DEADROSE6/FdD_Equipo_8/FundDiseño/Talleres/Taller_10/Onshape Areche Angello/bryam-areche-4c7b2a17-952c-4959-8db5-8d5ba8efbf5f-certificate.pdf

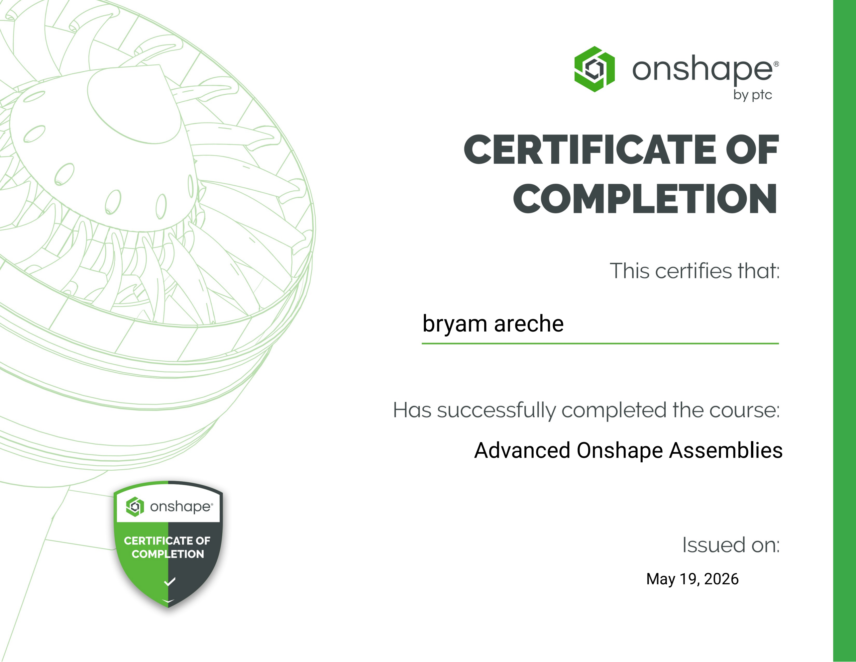
[picture p7: page 1]

bryam areche

Advanced Onshape Assemblies

May 19, 2026
