DEADROSE6/FdD_Equipo_8/Proyecto/MóduloMecánico/Certificados/Leslie Tomanguilla/CAD Basic.pdf

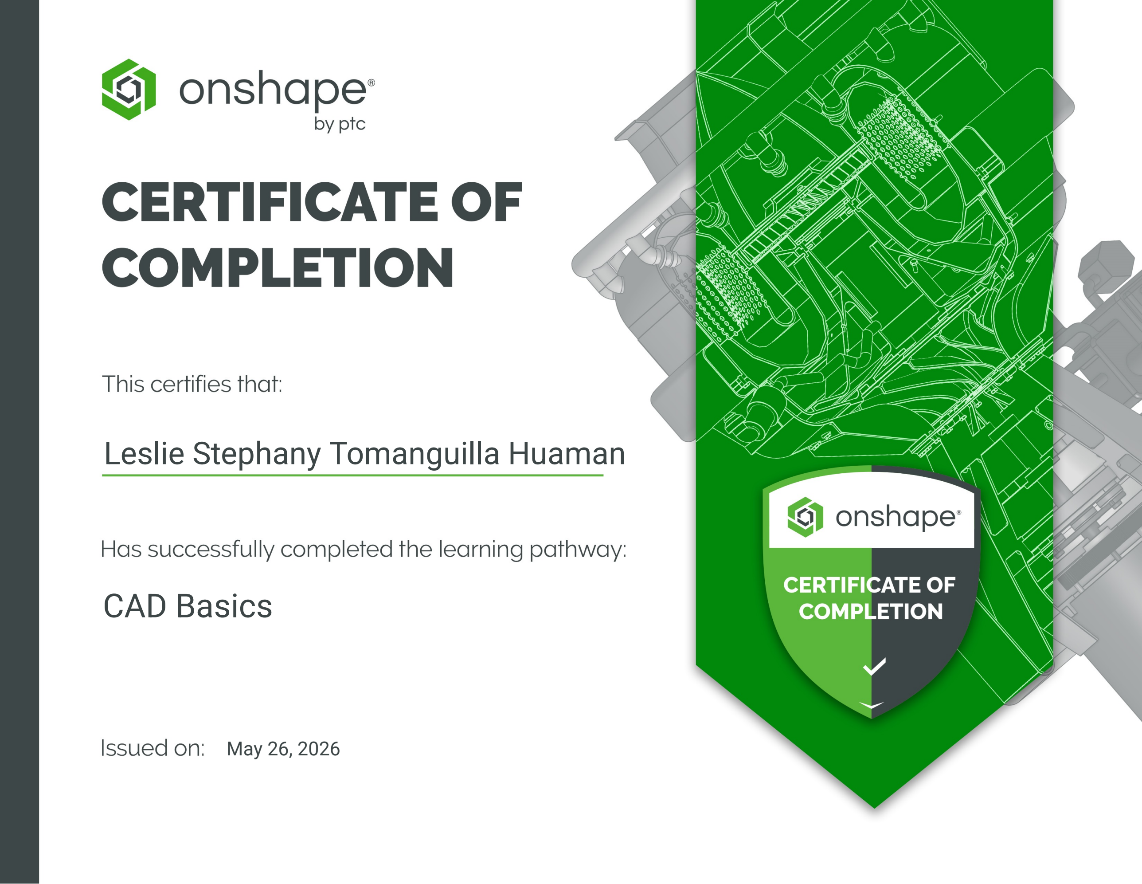
[picture p8: page 1]

Leslie Stephany Tomanguilla Huaman

CAD Basics

May 26, 2026
