DEADROSE6/FdD_Equipo_8/Proyecto/MóduloMecánico/Certificados/Daniela Mori/introduction-to-onshape-mori.pdf

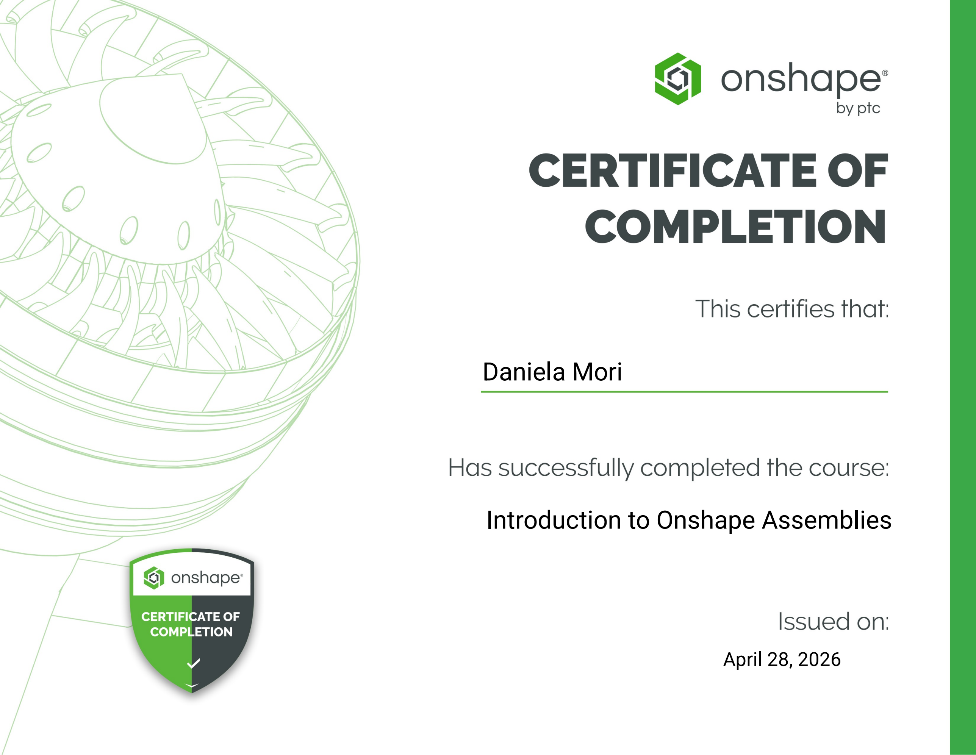
[picture p9: page 1]

Daniela Mori

April 28, 2026

Introduction to Onshape Assemblies
