DEADROSE6/FdD_Equipo_8/Proyecto/MóduloMecánico/Certificados/Leslie Tomanguilla/Advanced Onshape Assamblies.pdf

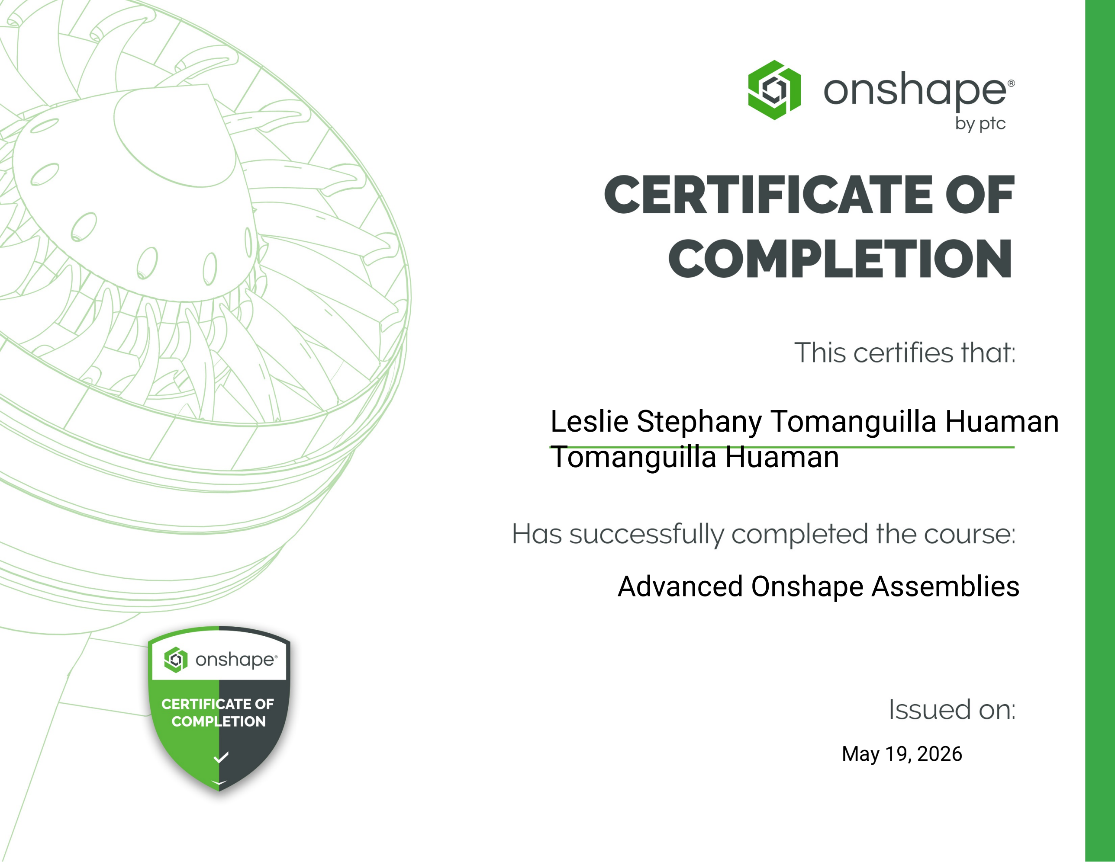
[picture p10: page 1]

Leslie Stephany Tomanguilla Huaman Tomanguilla Huaman

Advanced Onshape Assemblies

May 19, 2026
