DEADROSE6/FdD_Equipo_8/Proyecto/MóduloMecánico/Certificados/Rolando Ronceros/Advanced Onshape Assamblies.pdf

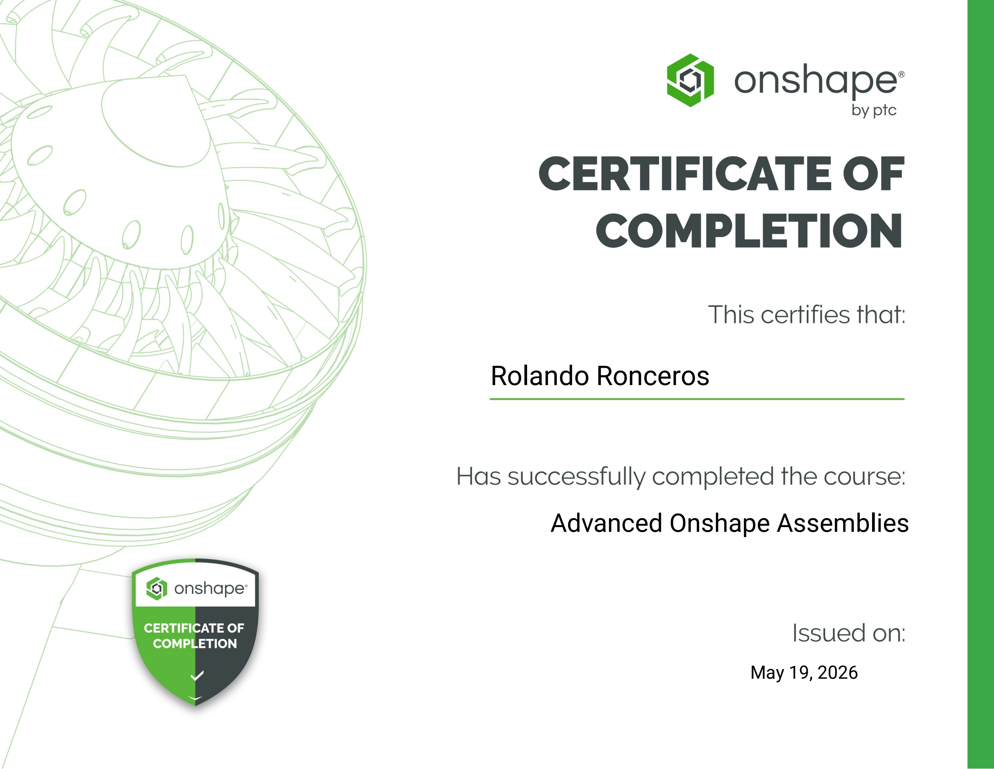
[picture p11: page 1]

Rolando Ronceros

Advanced Onshape Assemblies

May 19, 2026
