DEADROSE6/FdD_Equipo_8/Proyecto/MóduloMecánico/Certificados/Daniela Mori/CAD-Basics-mori.pdf

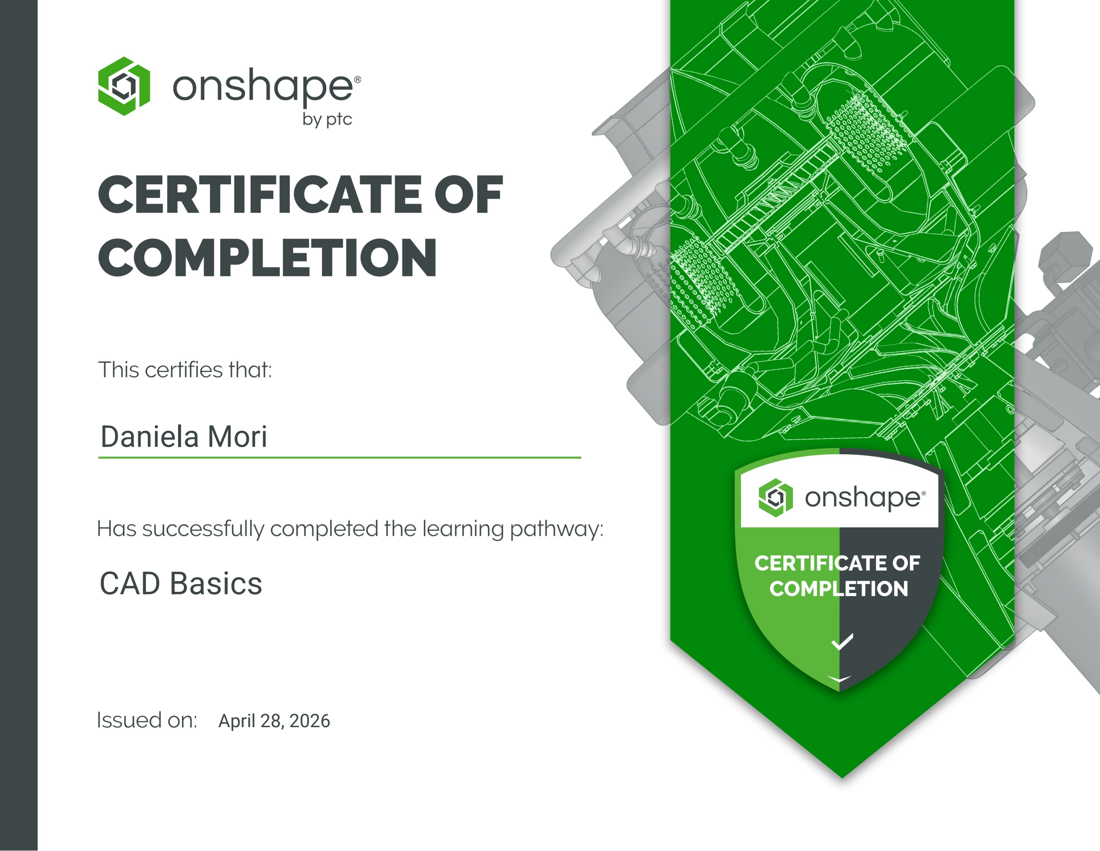
[picture p12: page 1]

## Daniela Mori

# CAD Basics

April 28, 2026
