DEADROSE6/FdD_Equipo_8/Proyecto/MóduloMecánico/Certificados/Rolando Ronceros/CAD Basic (1).pdf

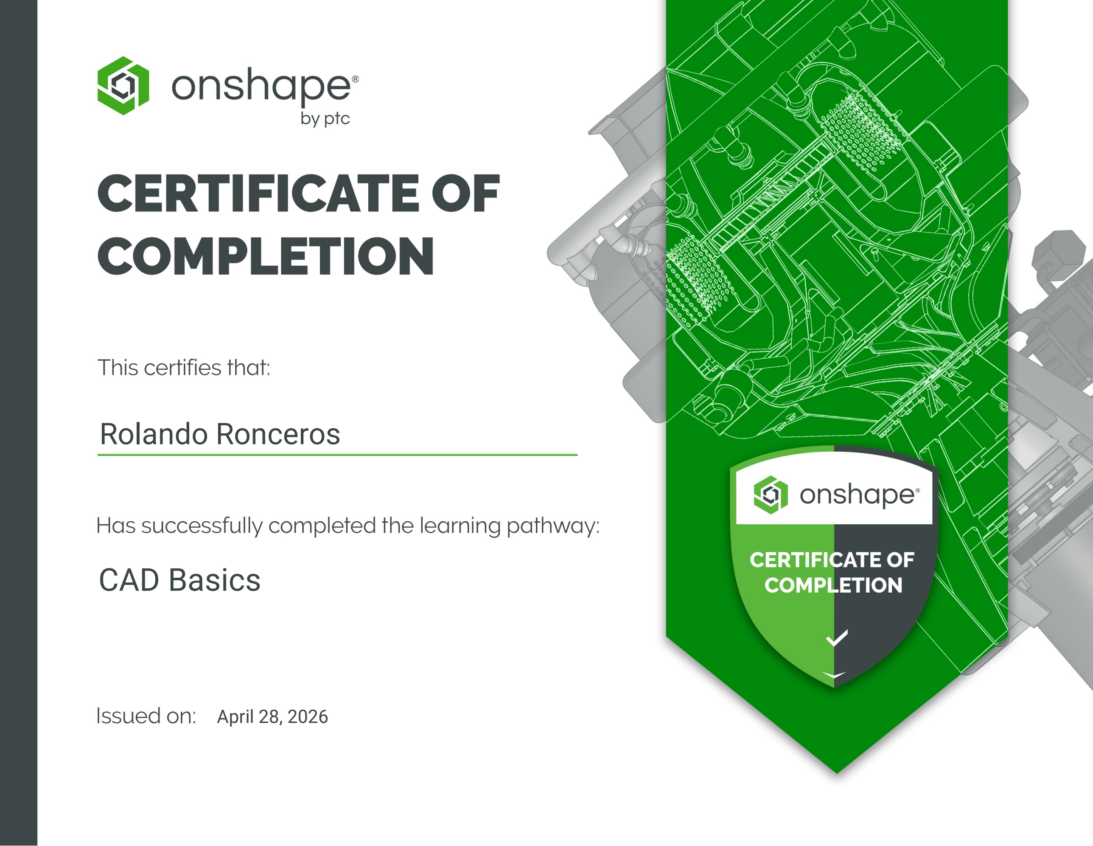
[picture p13: page 1]

Rolando Ronceros

CAD Basics

April 28, 2026
