DEADROSE6/FdD_Equipo_8/Proyecto/MóduloMecánico/Certificados/Alex Ccoyllo/CAD Basic.pdf

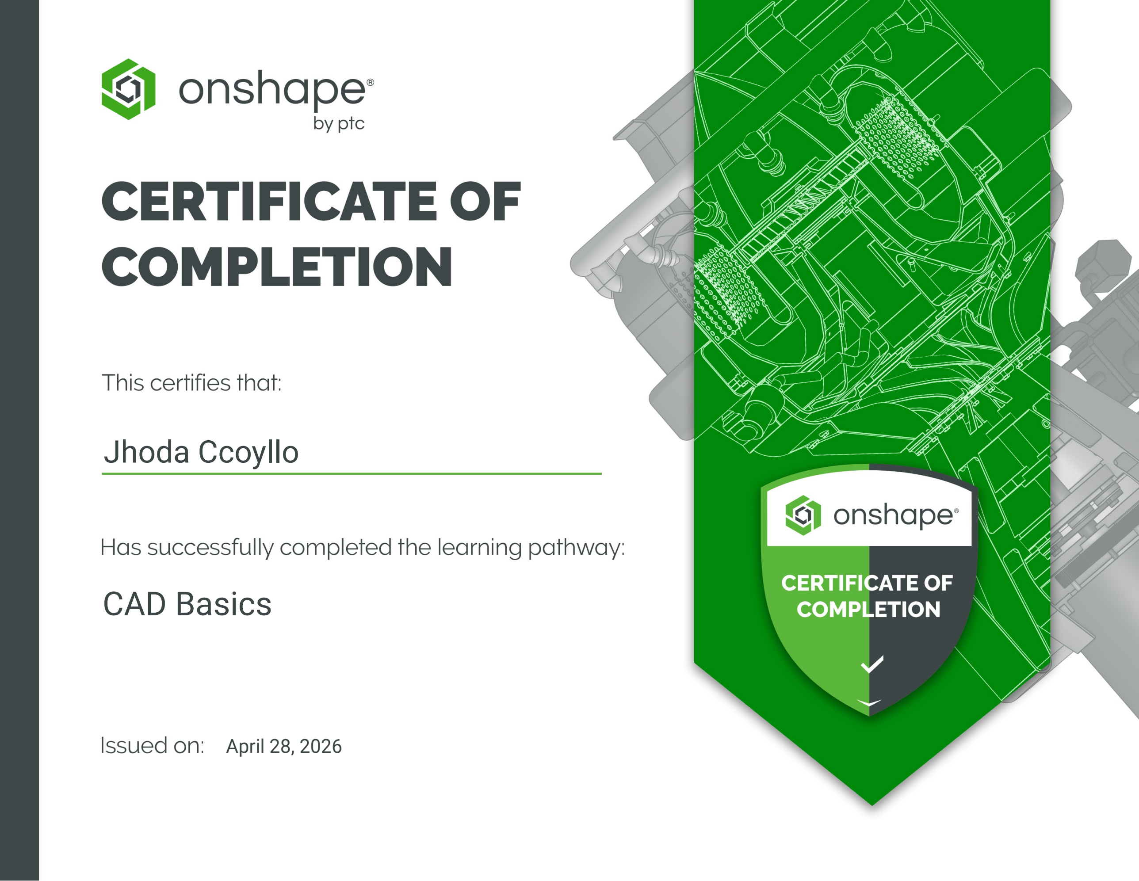
[picture p14: page 1]

## Jhoda Ccoyllo

# CAD Basics

April 28, 2026
