DEADROSE6/FdD_Equipo_8/FundDiseño/Entregables/Entregables_3/Bocetos/Prompt del Boceto (1).pdf

Dibujo técnico simple en blanco y negro sobre fondo completamente blanco, estilo boceto de ingeniería hecho a mano con líneas limpias. Mostrar tres vistas separadas de una caja electrónica.

Primera vista (vista frontal interna): caja rectangular abierta vista desde arriba. Señalar con flechas y texto los componentes: 'Amplificador de audio (PAM8403)' ubicado en el centro-izquierda, 'DF Player MP3' en la parte superior derecha de una placa central, 'Sensor de distancia (VL53L1X)' debajo a la derecha del PAM8403 y 'Sensor de presencia humana (LD2410C)' en la parte inferior. Mantener diseño simple y esquemático.

Segunda vista (Vista lateral derecho): vista lateral de la caja mostrando rejillas de ventilación y un altavoz circular. Señalar únicamente 'Altavoz'. Título arriba: 'Vista lateral derecho'.

Tercera vista (Vista isométrica): perspectiva isométrica de la misma caja mostrando los componentes internos. Añadir una flecha apuntando a una cámara con la etiqueta 'Cámara (OV3660) con XIAO SEED'. Título arriba: 'Vista isométrica'.

Estilo minimalista, líneas negras finas, sin colores, sin sombras, sin borde decorativo, sin marco rojo, aspecto de plano escolar limpio, distribución similar a un dibujo técnico realizado a lápiz sobre una hoja blanca.
