DEADROSE6/FdD_Equipo_8/FundDiseño/Talleres/Taller mecánico de ONSHAPE/Certificado de angello/Onshape_Fundamentals.pdf

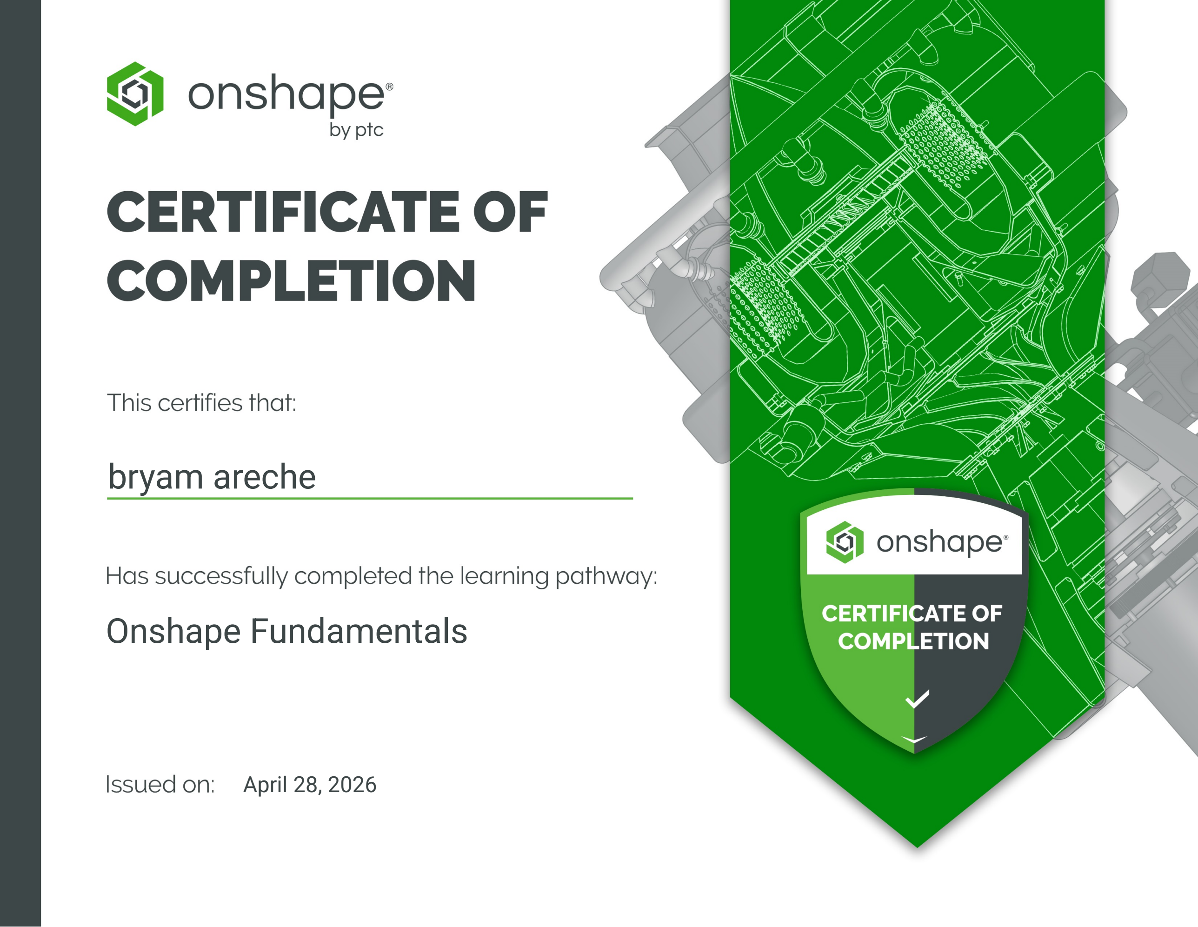
[picture p61: page 1]

Onshape Fundamentals

April 28, 2026

bryam areche
