DEADROSE6/FdD_Equipo_8/Recursos/Productos comerciales/Brochure2_WeWALK.pdf

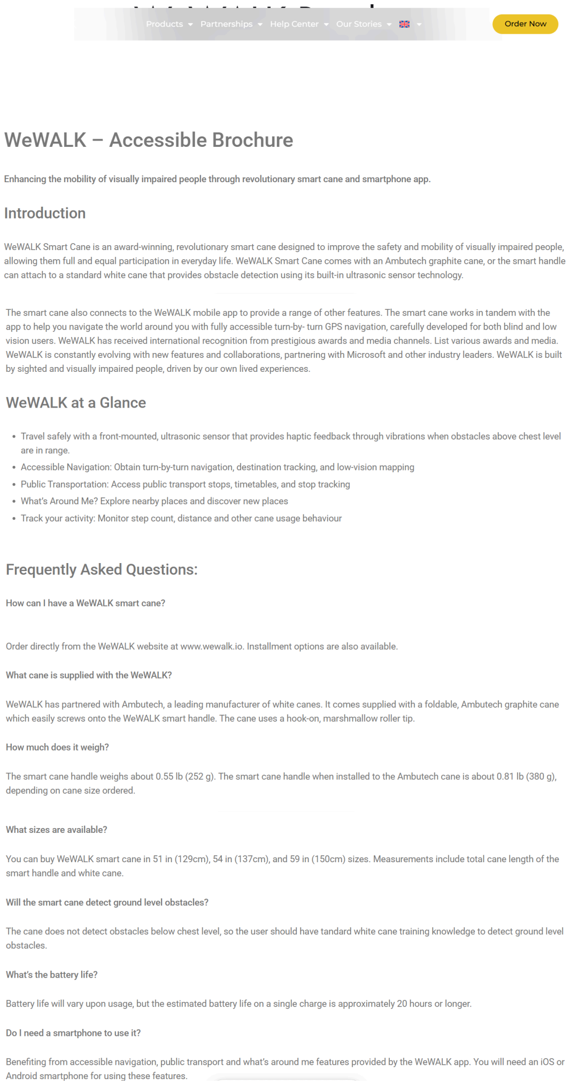
[picture p62: page 1]

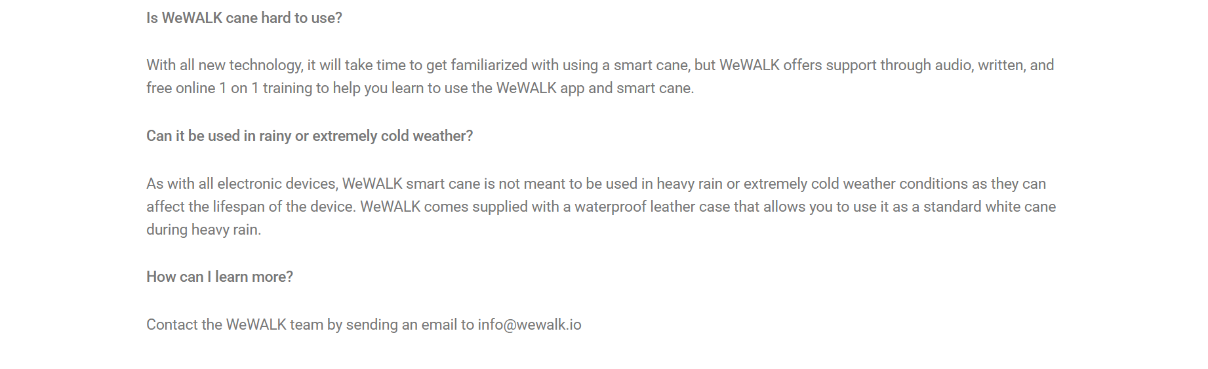
[picture p63: figure]
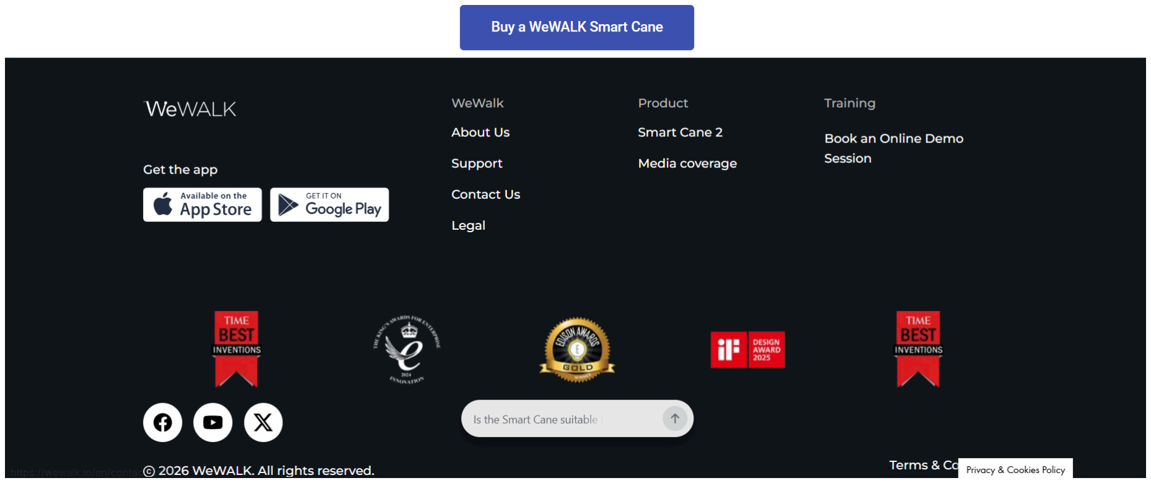
[picture p64: figure]
