DEADROSE6/FdD_Equipo_8/Proyecto/MóduloMecánico/V.FINAL/BocetoIA.pdf

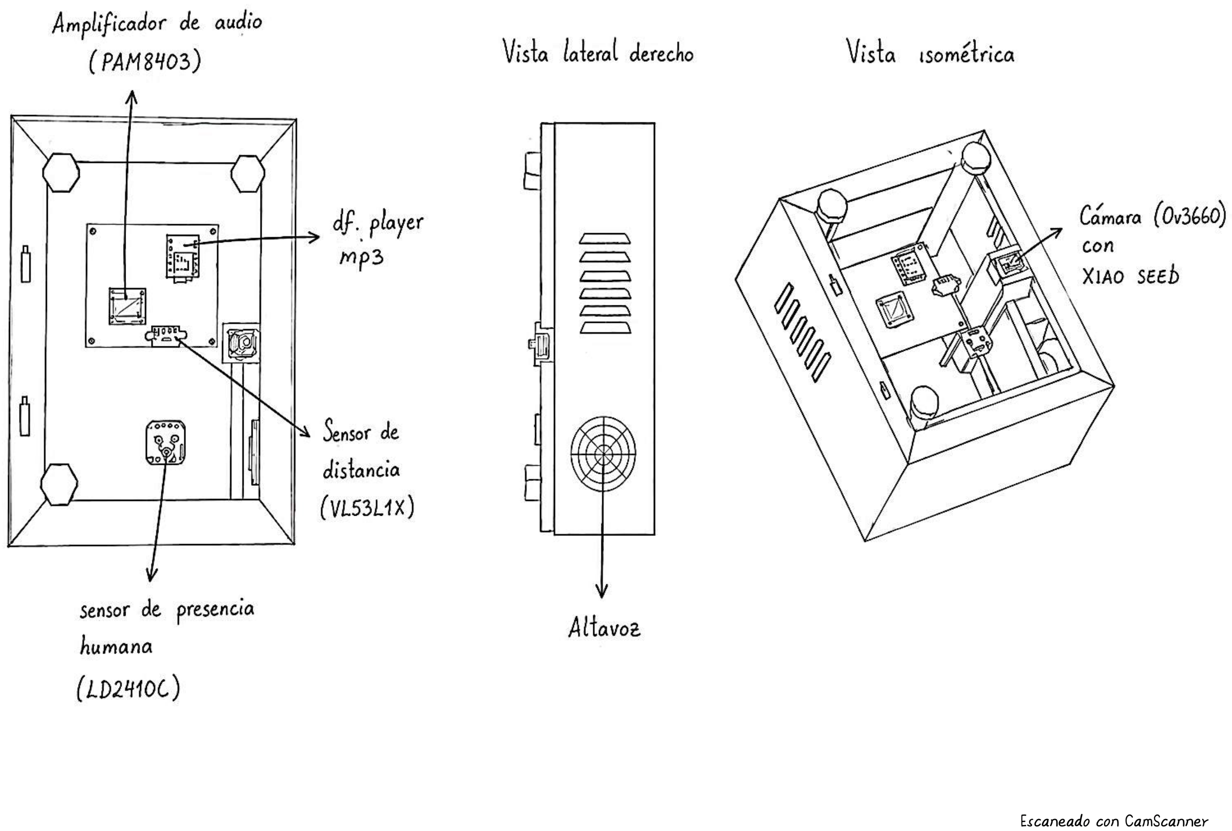
[picture p65: page 1]
