DEADROSE6/FdD_Equipo_8/Proyecto/MóduloMecánico/V.FINAL/BocetoIA2.pdf

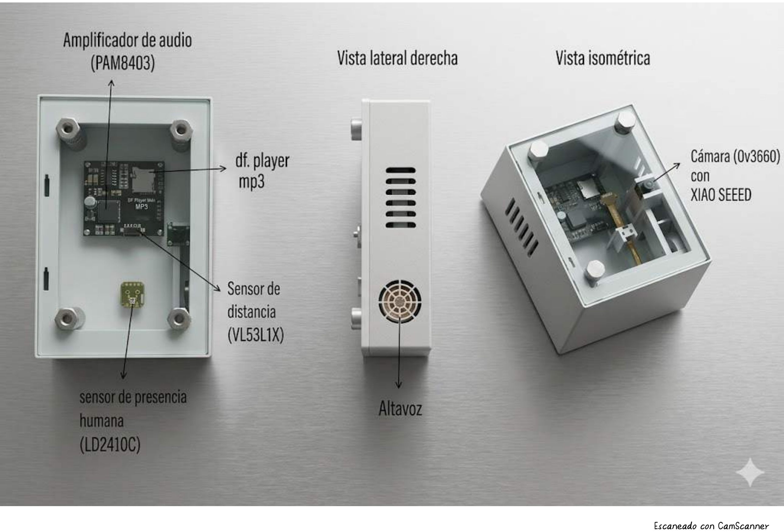
[picture p66: page 1]
