DEADROSE6/FdD_Equipo_8/Proyecto/MóduloMecánico/V.FINAL/BocetoLapiz.pdf

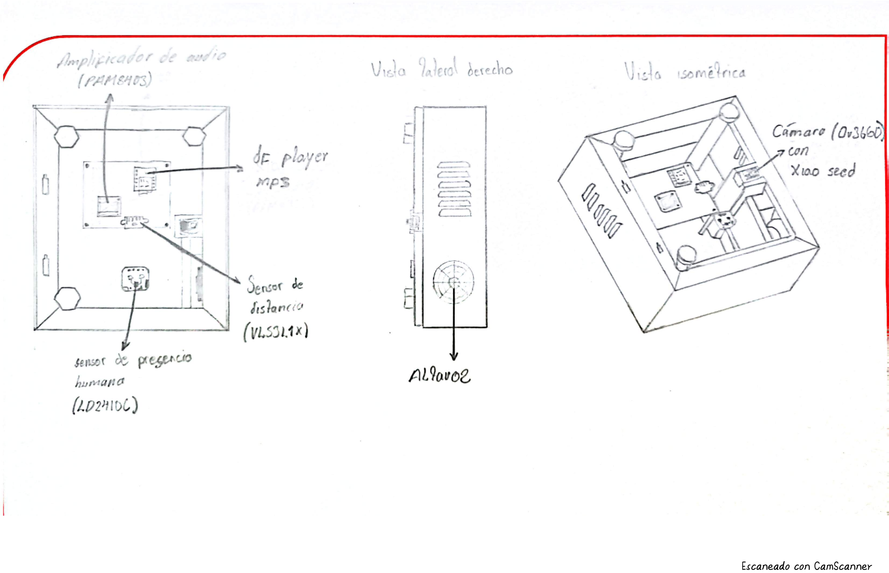
[picture p67: page 1]
