DEADROSE6/FdD_Equipo_8/Proyecto/MóduloMecánico/Certificados/Leslie Tomanguilla/Detailed Drawings.pdf

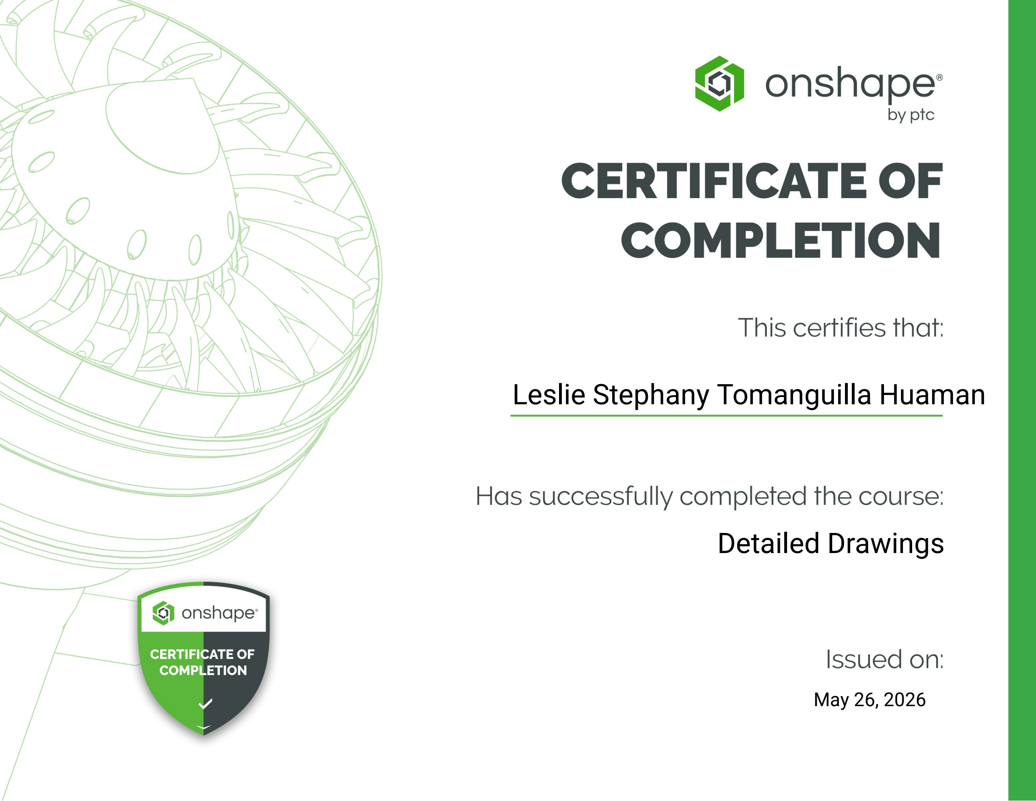
[picture p68: page 1]

Leslie Stephany Tomanguilla Huaman

May 26, 2026

Detailed Drawings
