DEADROSE6/FdD_Equipo_8/Proyecto/MóduloMecánico/Certificados/Leslie Tomanguilla/Introduction to Drawings.pdf

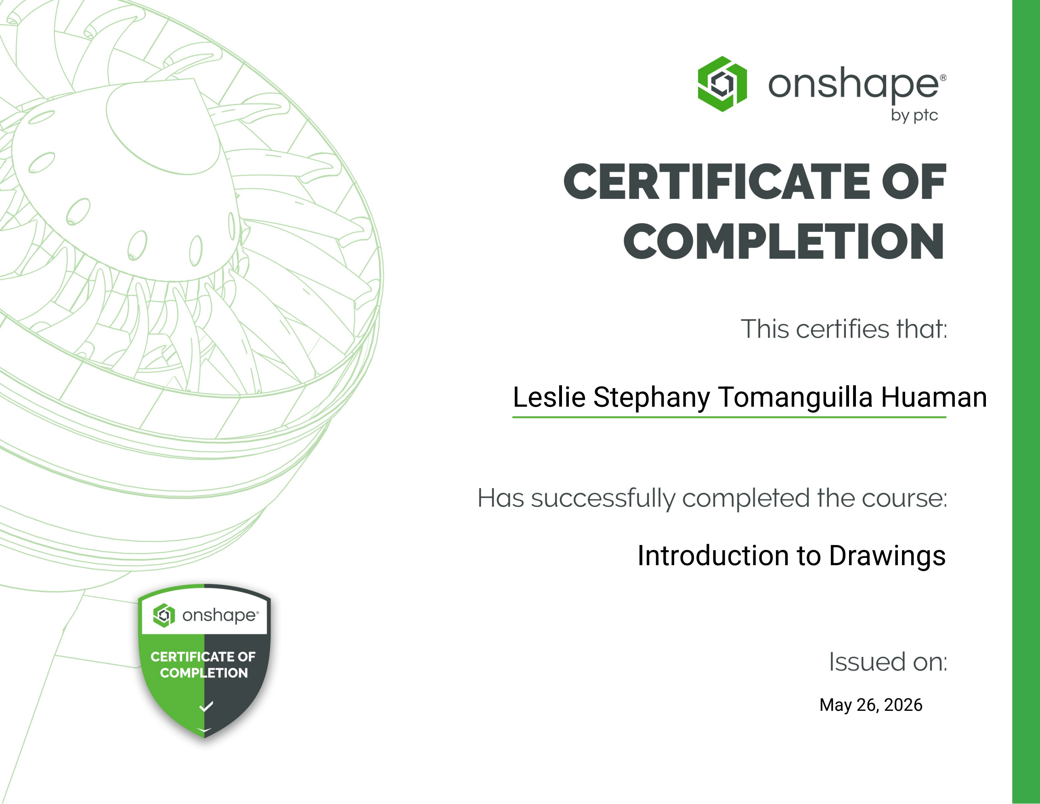
[picture p69: page 1]

Leslie Stephany Tomanguilla Huaman

May 26, 2026

Introduction to Drawings
