DEADROSE6/FdD_Equipo_8/Proyecto/MóduloMecánico/Certificados/Leslie Tomanguilla/Introduction to Part Studios.pdf

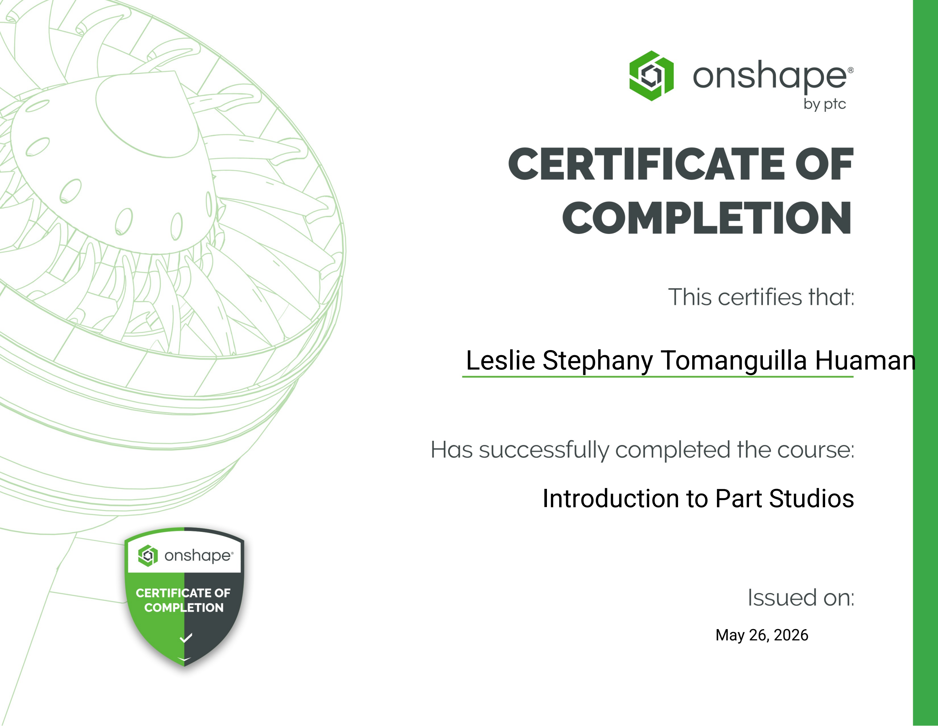
[picture p70: page 1]

Leslie Stephany Tomanguilla Huaman

Introduction to Part Studios

May 26, 2026
