DEADROSE6/FdD_Equipo_8/Proyecto/MóduloMecánico/Certificados/Leslie Tomanguilla/Introduction to Sketching.pdf

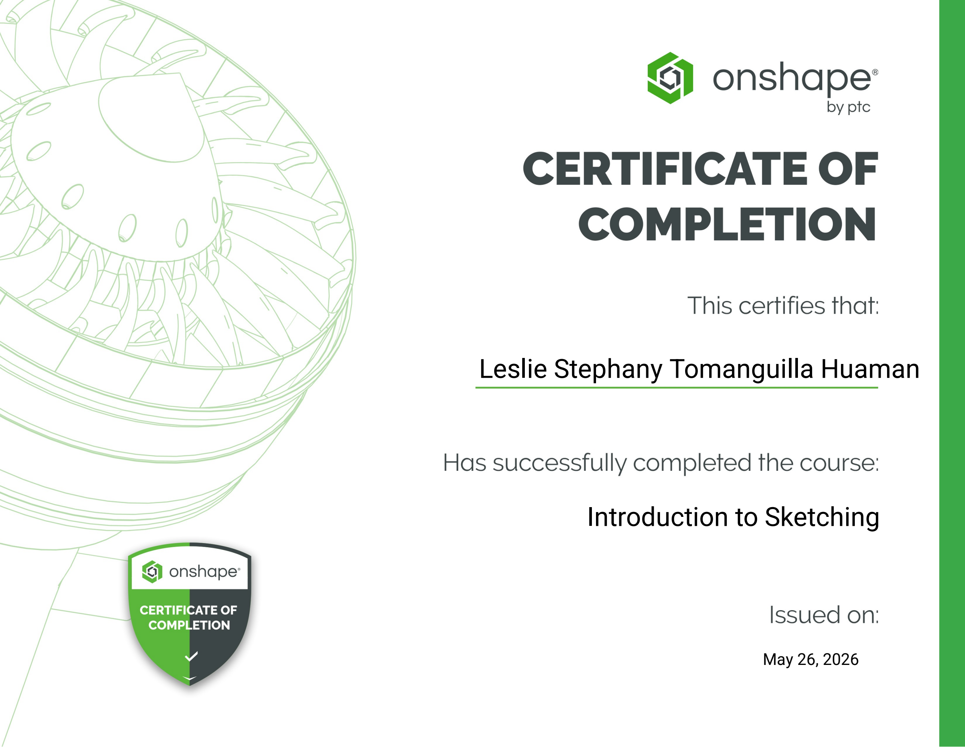
[picture p71: page 1]

Leslie Stephany Tomanguilla Huaman

Introduction to Sketching

May 26, 2026
