DEADROSE6/FdD_Equipo_8/Proyecto/MóduloMecánico/Certificados/Leslie Tomanguilla/Onshape Fundamentals.pdf

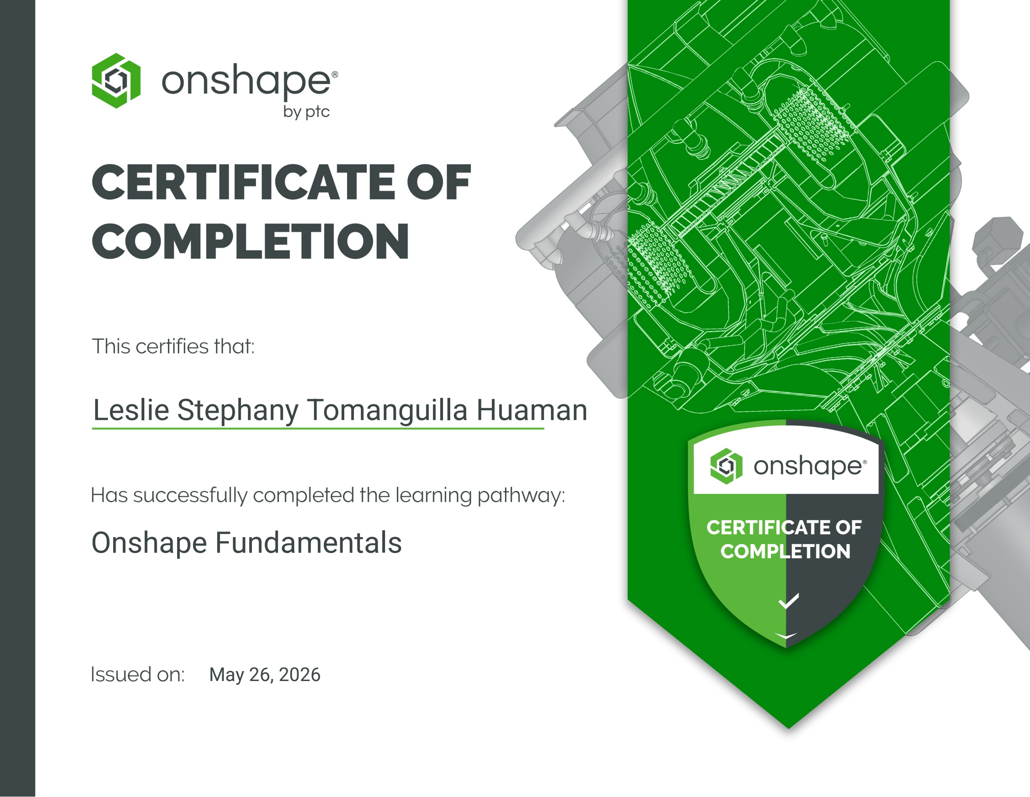
[picture p72: page 1]

Onshape Fundamentals

May 26, 2026

Leslie Stephany Tomanguilla Huaman
