DEADROSE6/FdD_Equipo_8/Proyecto/MóduloMecánico/Certificados/Daniela Mori/detailed-drawings-mori.pdf

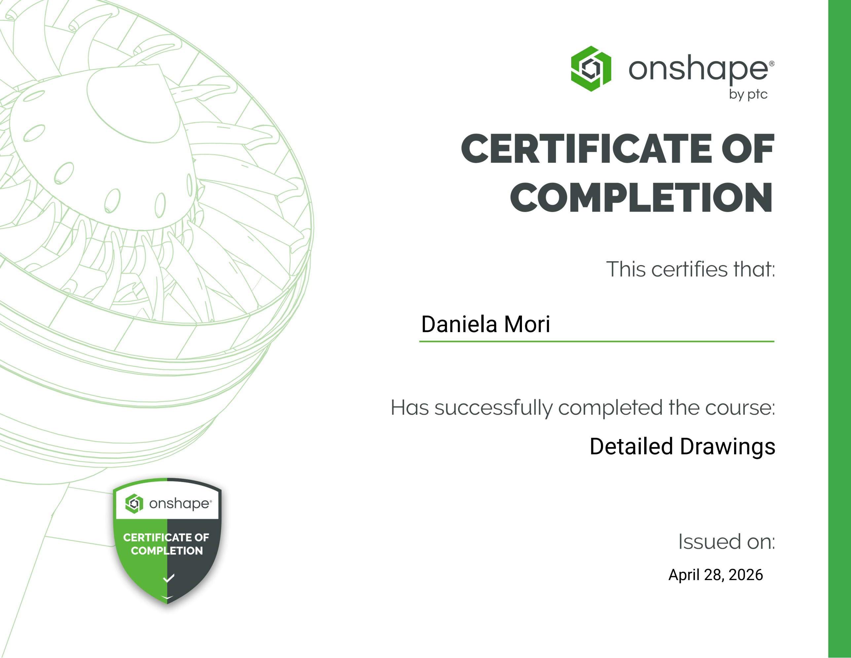
[picture p73: page 1]

Daniela Mori

April 28, 2026

Detailed Drawings
