DEADROSE6/FdD_Equipo_8/Proyecto/MóduloMecánico/Certificados/Daniela Mori/introduccion-to-drawings-mori.pdf

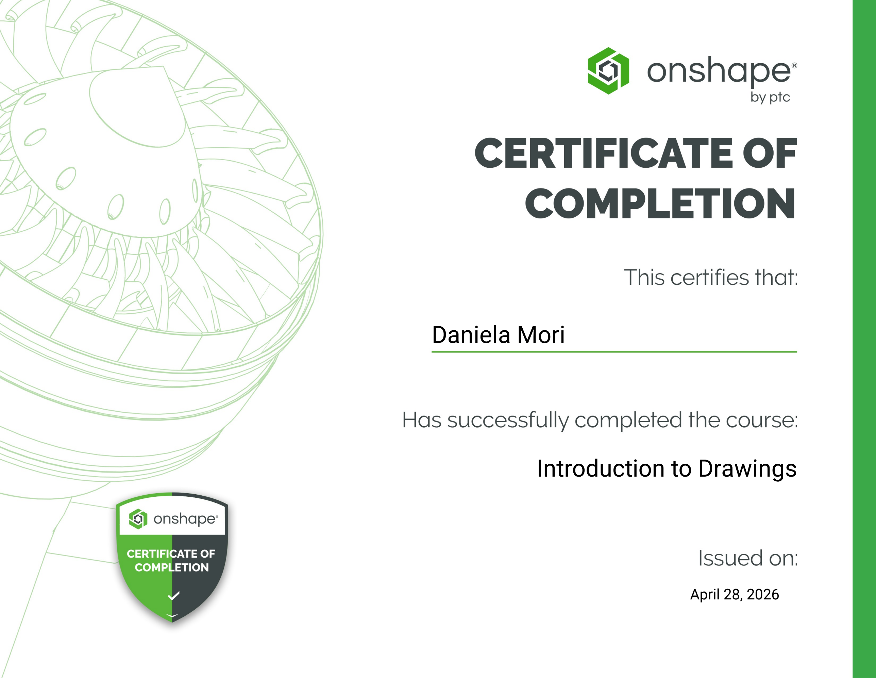
[picture p74: page 1]

Daniela Mori

April 28, 2026

Introduction to Drawings
