DEADROSE6/FdD_Equipo_8/Proyecto/MóduloMecánico/Certificados/Daniela Mori/Introduction to Part Studios-mori.pdf

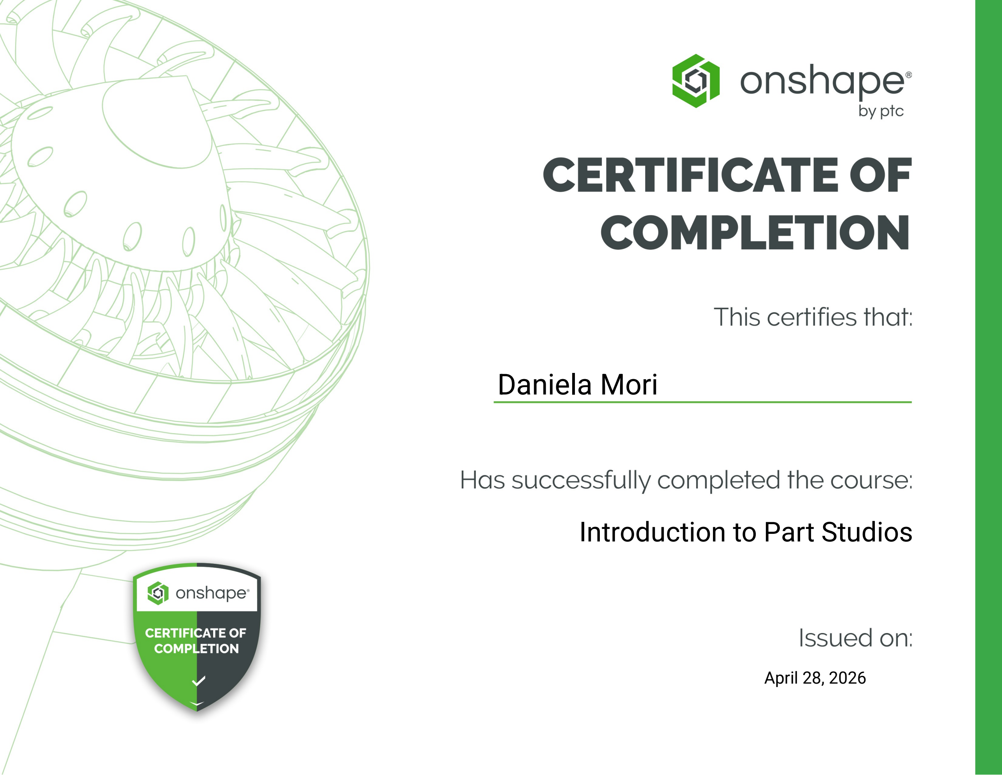
[picture p75: page 1]

Daniela Mori

Introduction to Part Studios

April 28, 2026
