DEADROSE6/FdD_Equipo_8/Proyecto/MóduloMecánico/Certificados/Daniela Mori/introduction-to-skeching-mori.pdf

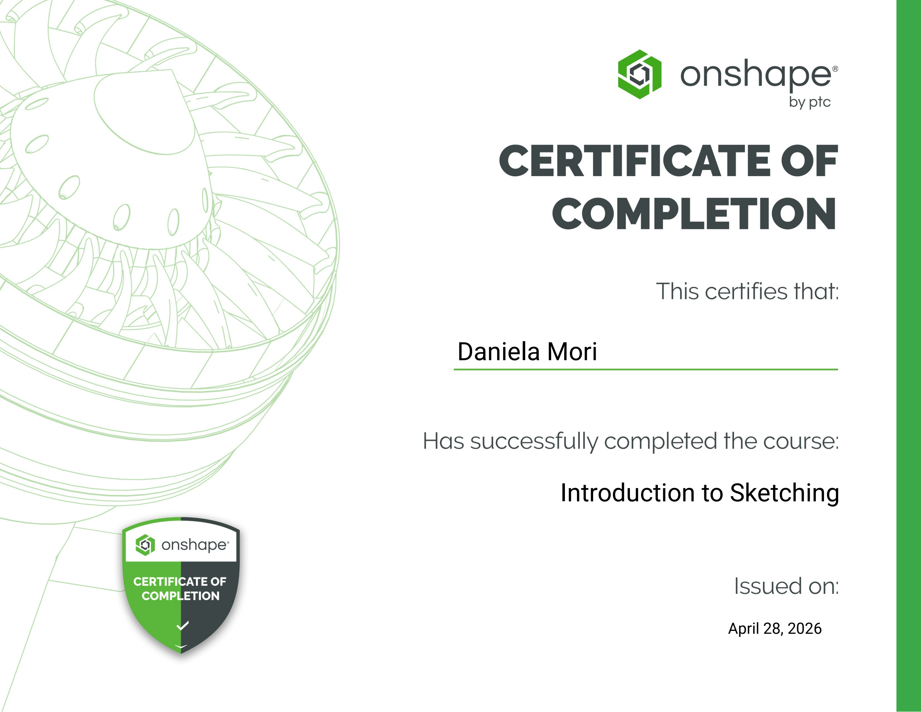
[picture p76: page 1]

Daniela Mori

Introduction to Sketching

April 28, 2026
