DEADROSE6/FdD_Equipo_8/Proyecto/MóduloMecánico/Certificados/Alex Ccoyllo/Detailed Drawings.pdf

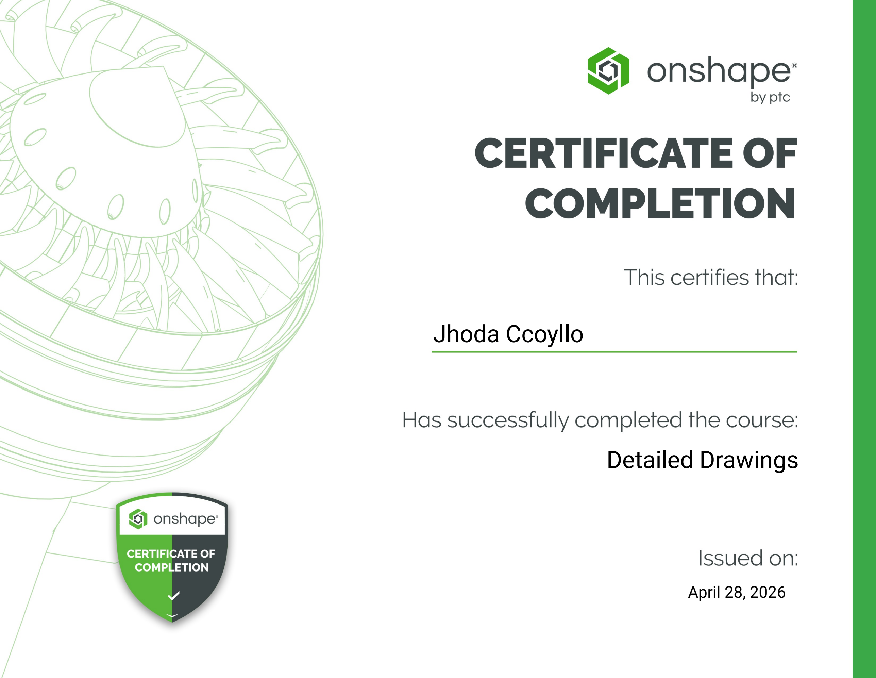
[picture p77: page 1]

Jhoda Ccoyllo

April 28, 2026

Detailed Drawings
