DEADROSE6/FdD_Equipo_8/Proyecto/MóduloMecánico/Certificados/Alex Ccoyllo/Introduction  to Sketching.pdf

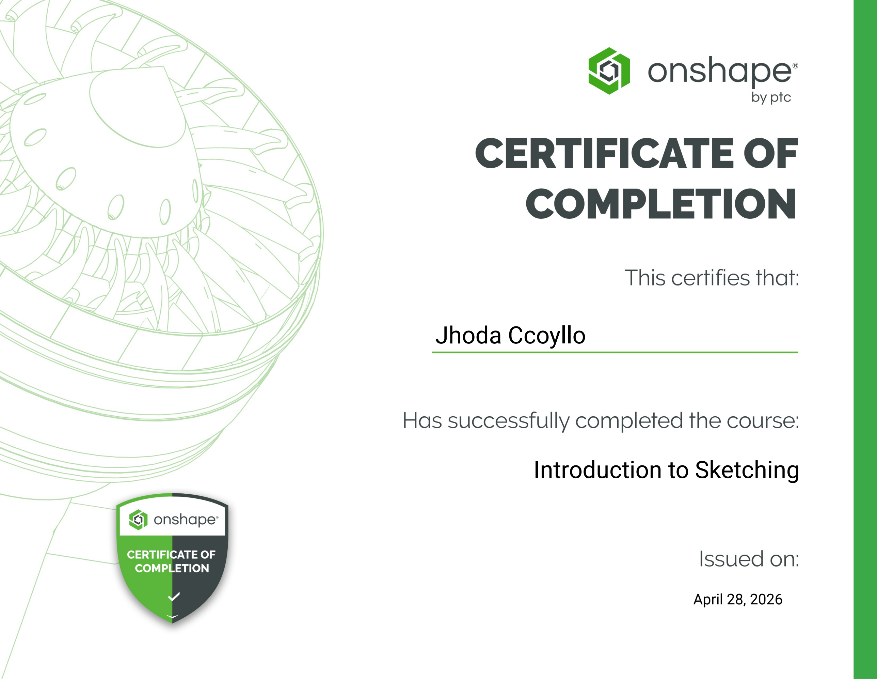
[picture p78: page 1]

Jhoda Ccoyllo

Introduction to Sketching

April 28, 2026
