DEADROSE6/FdD_Equipo_8/Proyecto/MóduloMecánico/Certificados/Alex Ccoyllo/Introductionto Drawings.pdf

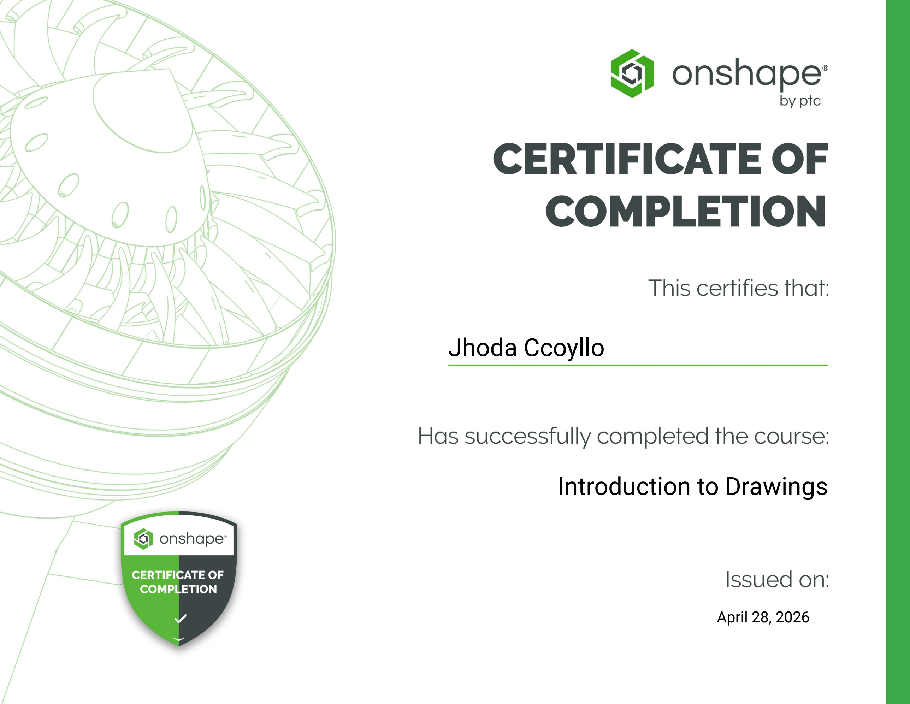
[picture p79: page 1]

Jhoda Ccoyllo

April 28, 2026

Introduction to Drawings
