DEADROSE6/FdD_Equipo_8/Proyecto/MóduloMecánico/Certificados/Alex Ccoyllo/Introductionto Part Studios.pdf

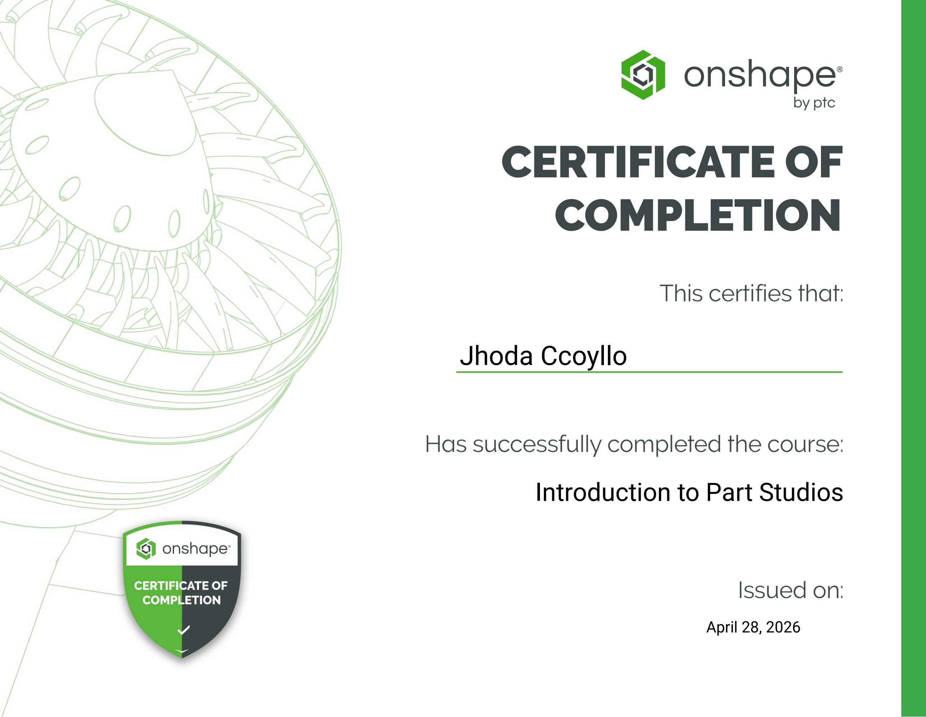
[picture p80: page 1]

Jhoda Ccoyllo

Introduction to Part Studios

April 28, 2026
