DEADROSE6/FdD_Equipo_8/Proyecto/MóduloMecánico/Certificados/Rolando Ronceros/Detailed Drawings (1).pdf

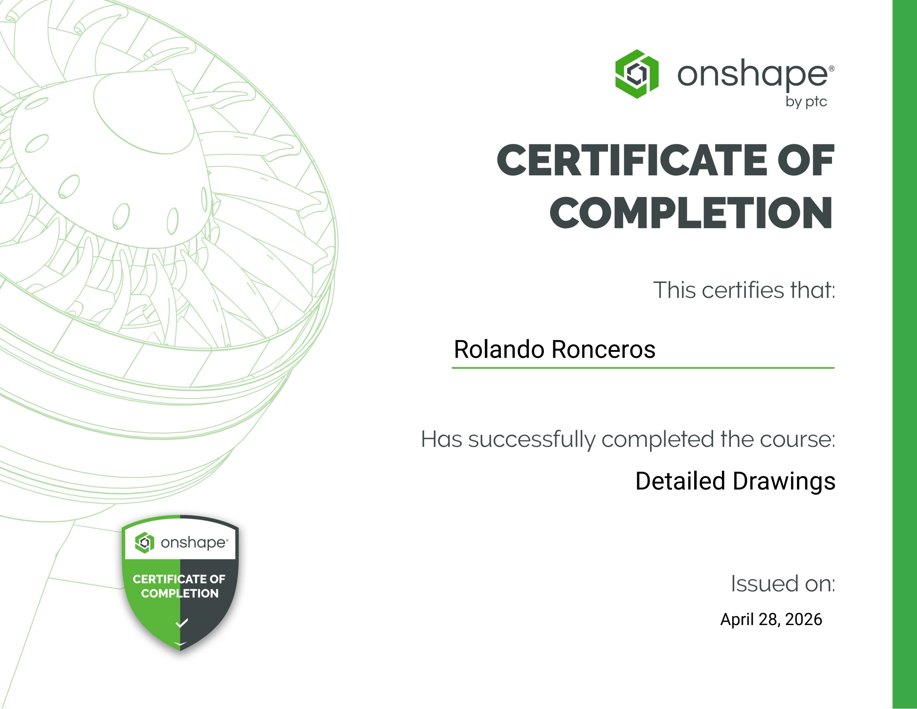
[picture p81: page 1]

Rolando Ronceros

April 28, 2026

Detailed Drawings
