DEADROSE6/FdD_Equipo_8/Proyecto/MóduloMecánico/Certificados/Rolando Ronceros/Introduction to Drawings.pdf

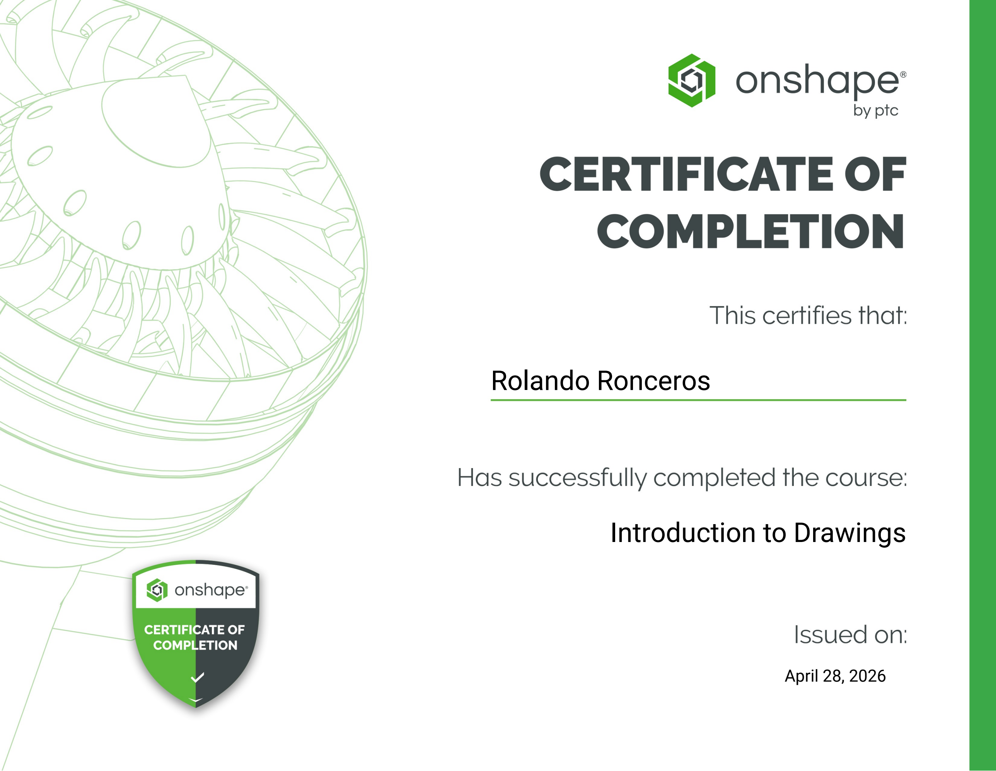
[picture p82: page 1]

Rolando Ronceros

April 28, 2026

Introduction to Drawings
