DEADROSE6/FdD_Equipo_8/Proyecto/MóduloMecánico/Certificados/Rolando Ronceros/Introduction to Part Studios.pdf

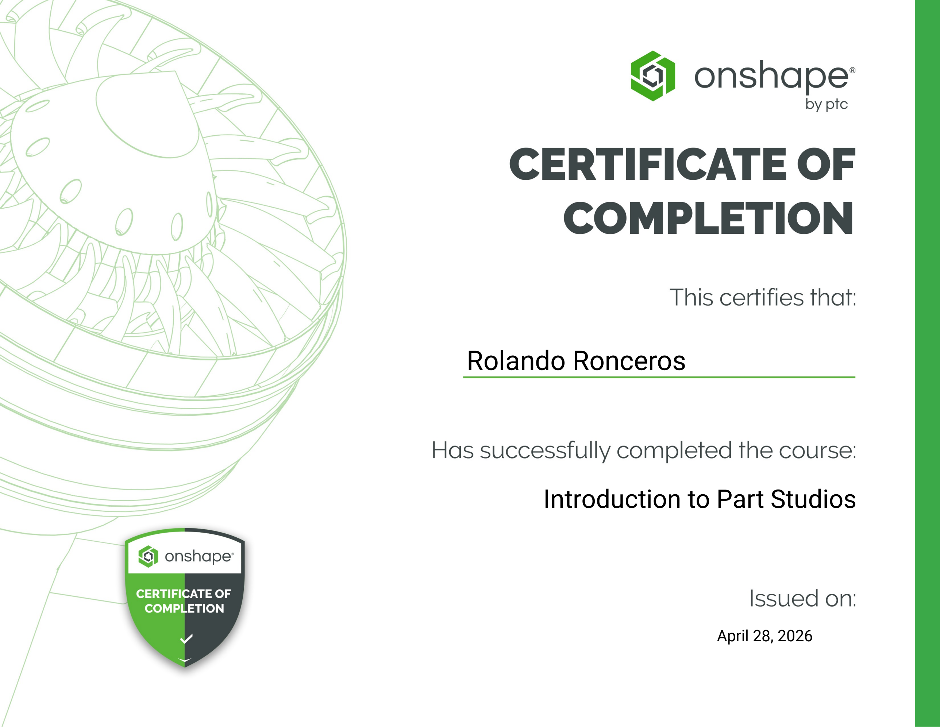
[picture p83: page 1]

Rolando Ronceros

Introduction to Part Studios

April 28, 2026
