DEADROSE6/FdD_Equipo_8/Proyecto/MóduloMecánico/Certificados/Rolando Ronceros/Introduction to Sketching.pdf

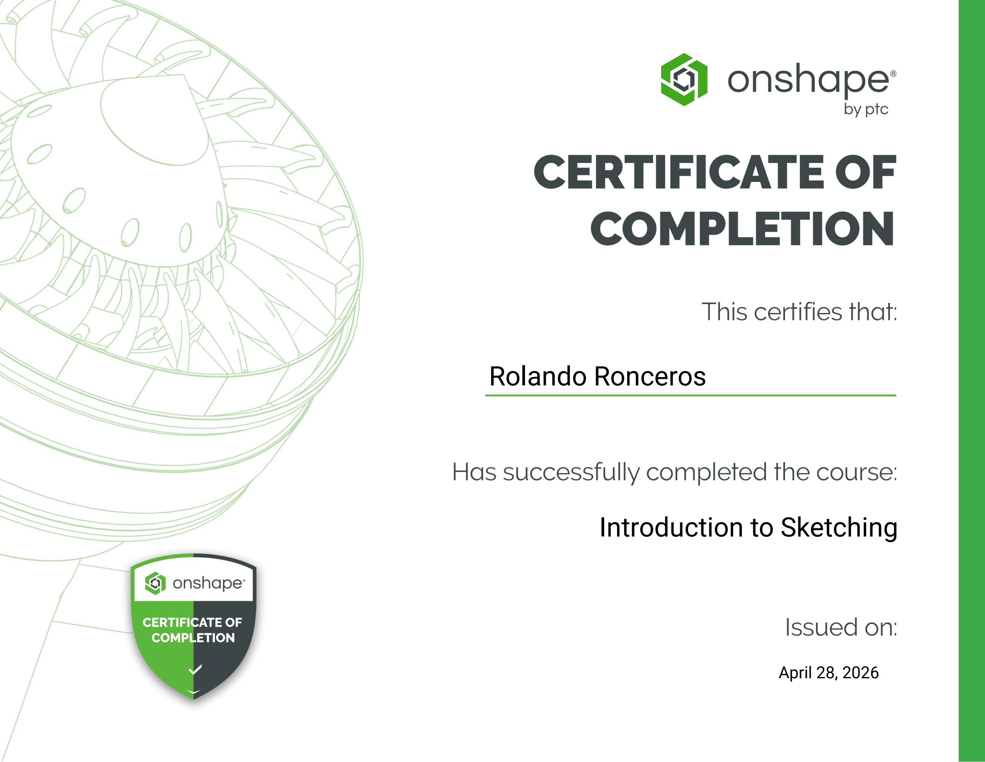
[picture p84: page 1]

Rolando Ronceros

Introduction to Sketching

April 28, 2026
