DEADROSE6/FdD_Equipo_8/Proyecto/MóduloMecánico/Certificados/Daniela Mori/onshape-fundamentals-mori.pdf

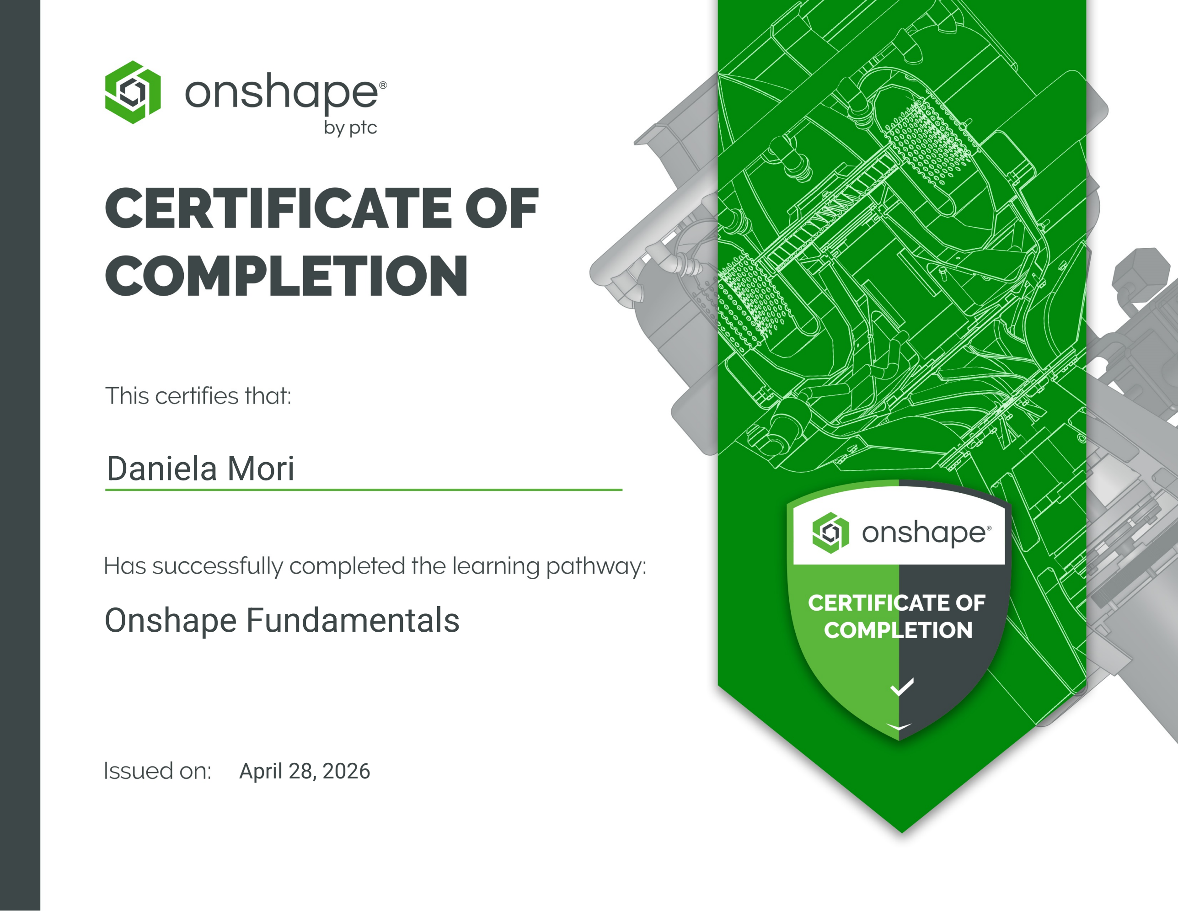
[picture p85: page 1]

Onshape Fundamentals

April 28, 2026

Daniela Mori
