DEADROSE6/FdD_Equipo_8/Proyecto/MóduloMecánico/Certificados/Rolando Ronceros/Onshape Fundamentals (1).pdf

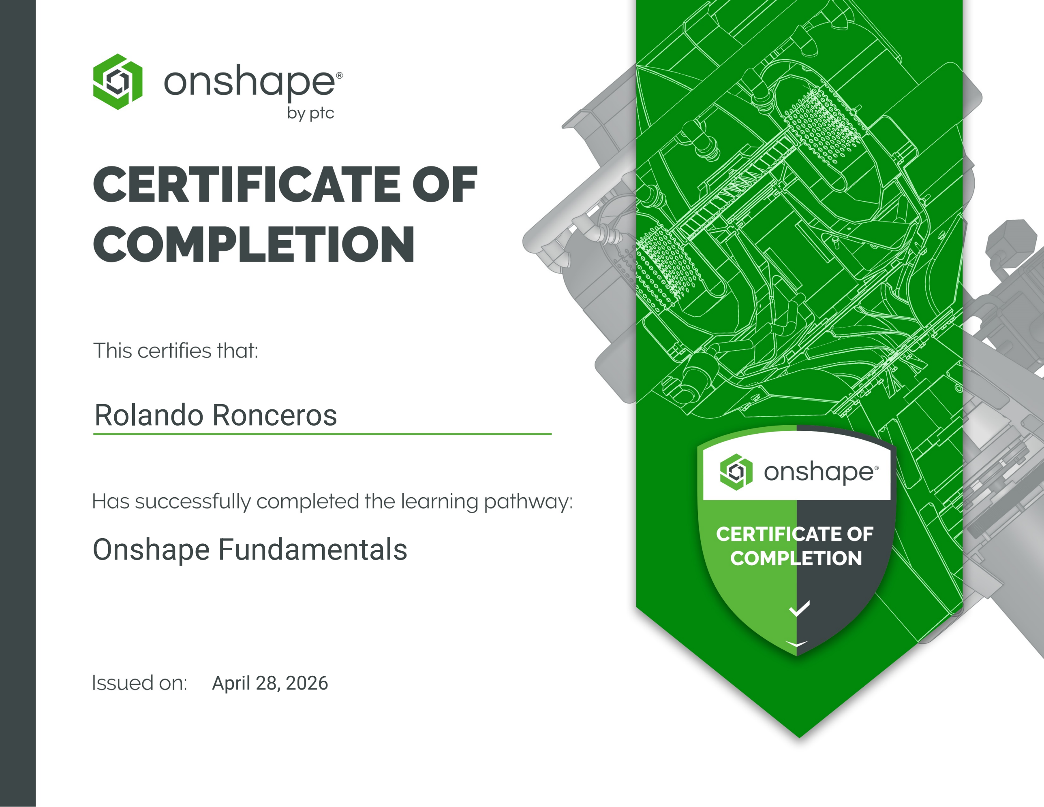
[picture p86: page 1]

Onshape Fundamentals

April 28, 2026

Rolando Ronceros
