DEADROSE6/FdD_Equipo_8/Proyecto/MóduloMecánico/Certificados/Alex Ccoyllo/Onshape Fundamentals.pdf

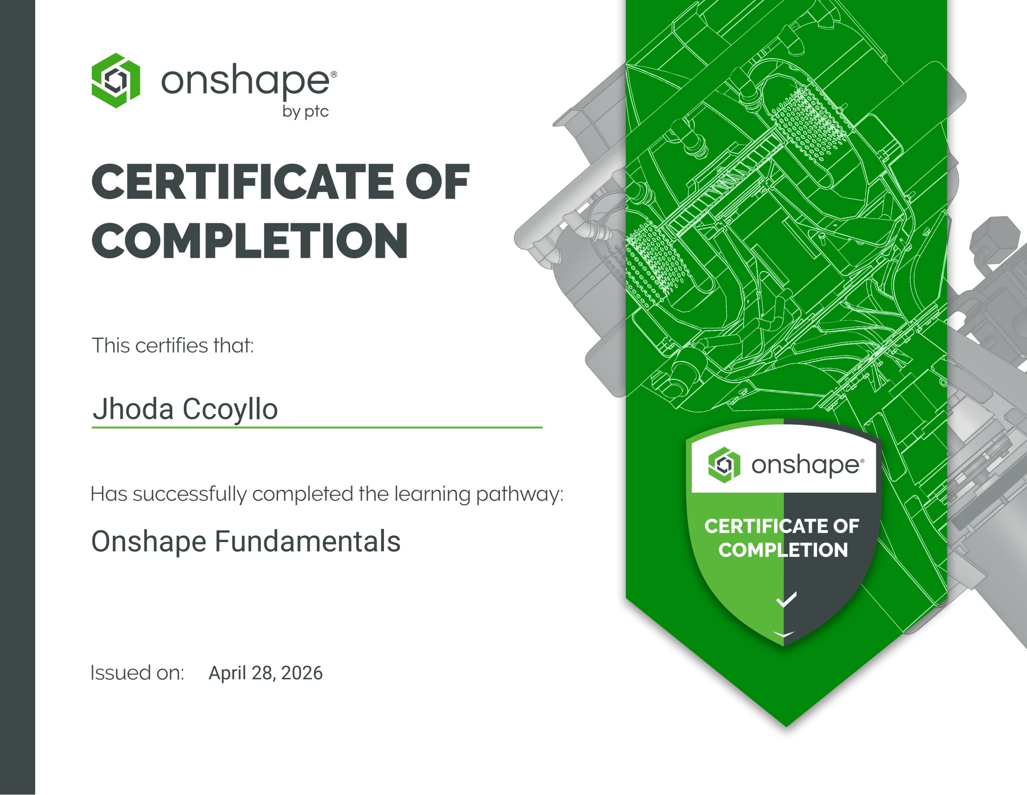
[picture p87: page 1]

Onshape Fundamentals

April 28, 2026

Jhoda Ccoyllo
