DEADROSE6/FdD_Equipo_8/FundDiseño/Talleres/Taller mecánico de ONSHAPE/Certificado de angello/Advanced Onshape Assamblies.pdf

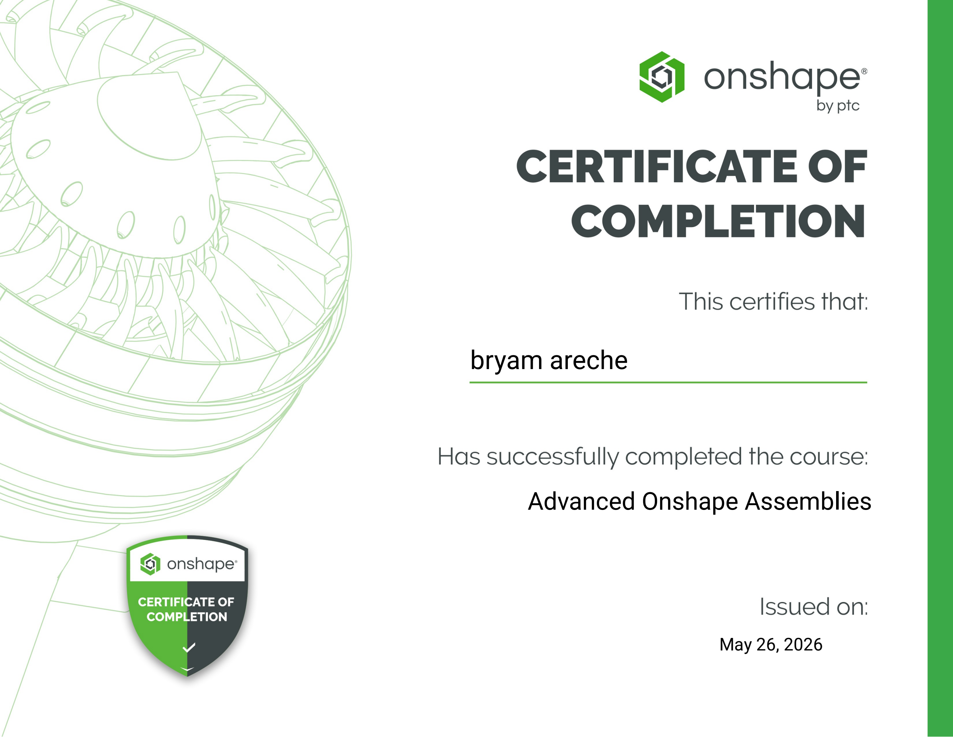
[picture p88: page 1]

bryam areche

Advanced Onshape Assemblies

May 26, 2026
