DEADROSE6/FdD_Equipo_8/FundDiseño/Talleres/Taller mecánico de ONSHAPE/Certificado de angello/CAD Basic.pdf

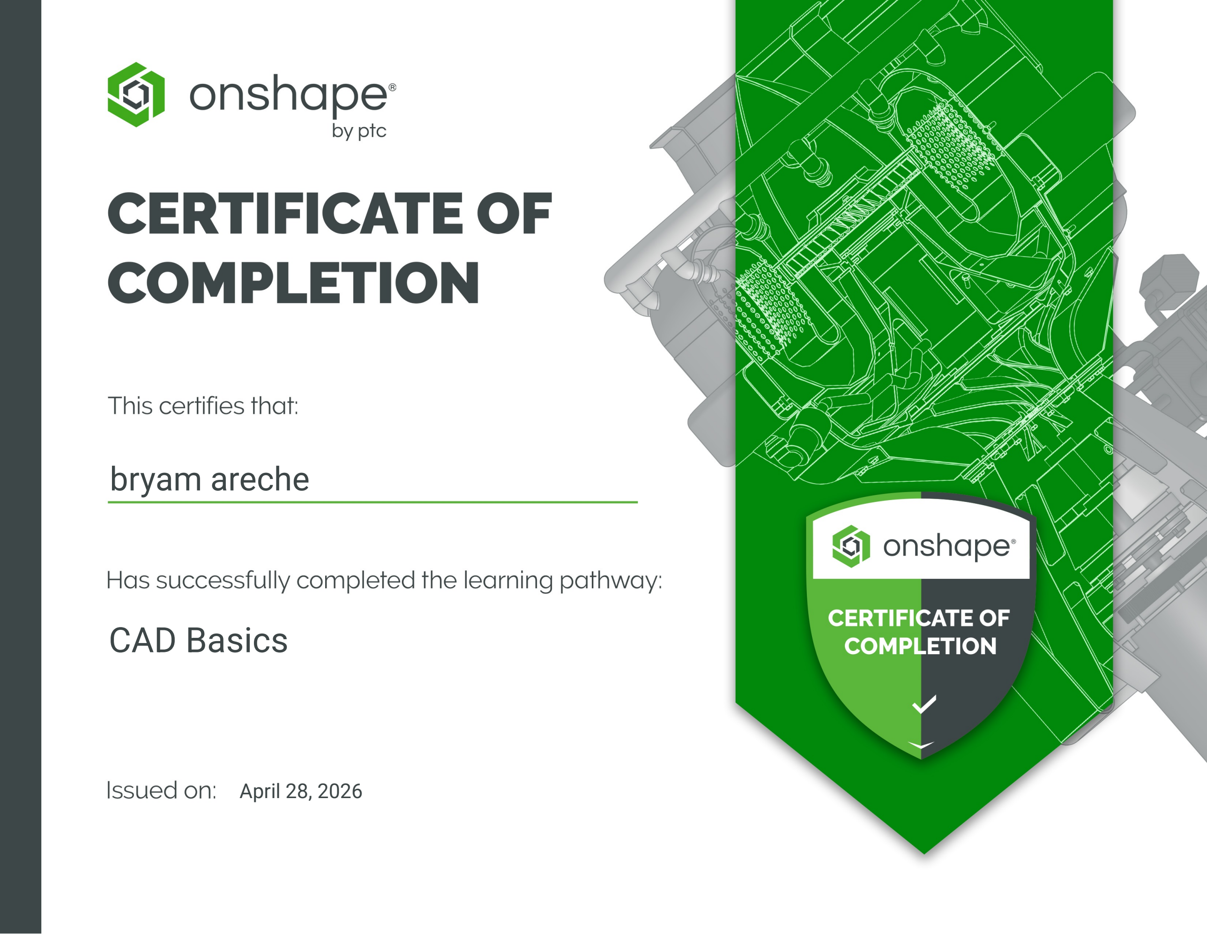
[picture p89: page 1]

## bryam areche

# CAD Basics

April 28, 2026
