DEADROSE6/FdD_Equipo_8/FundDiseño/Talleres/Taller mecánico de ONSHAPE/Certificado de angello/Detailed Drawings.pdf

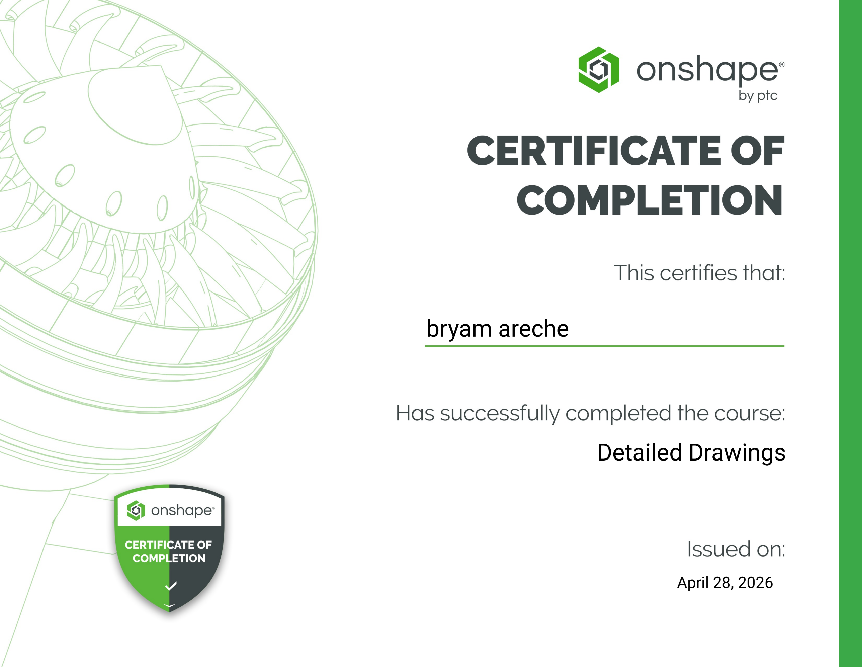
[picture p90: page 1]

bryam areche

April 28, 2026

Detailed Drawings
