DEADROSE6/FdD_Equipo_8/FundDiseño/Talleres/Taller mecánico de ONSHAPE/Certificado de angello/Introduction to Drawings.pdf

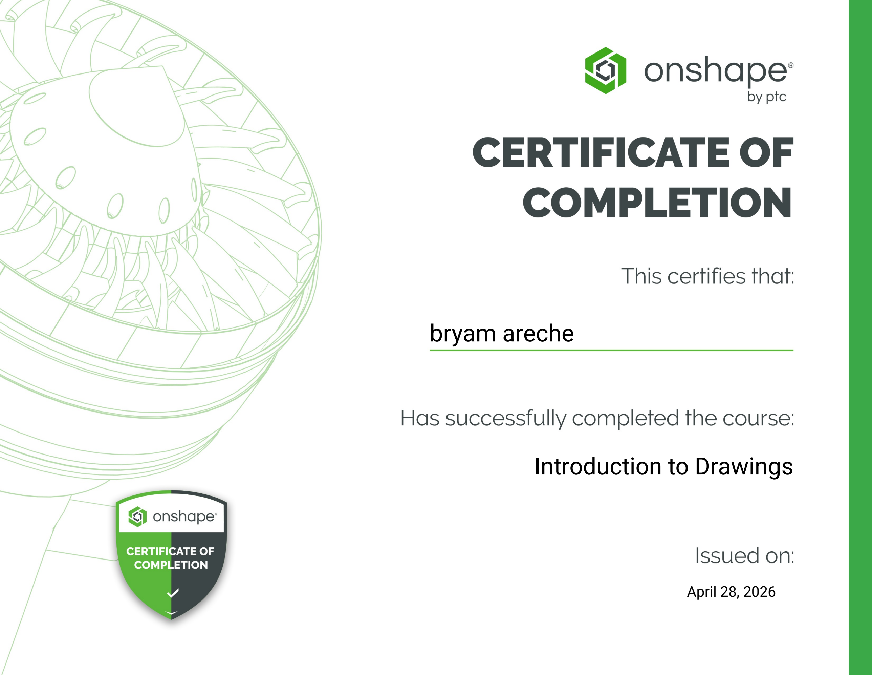
[picture p91: page 1]

bryam areche

April 28, 2026

Introduction to Drawings
