DEADROSE6/FdD_Equipo_8/FundDiseño/Talleres/Taller mecánico de ONSHAPE/Certificado de angello/Introduction to Part Studios.pdf

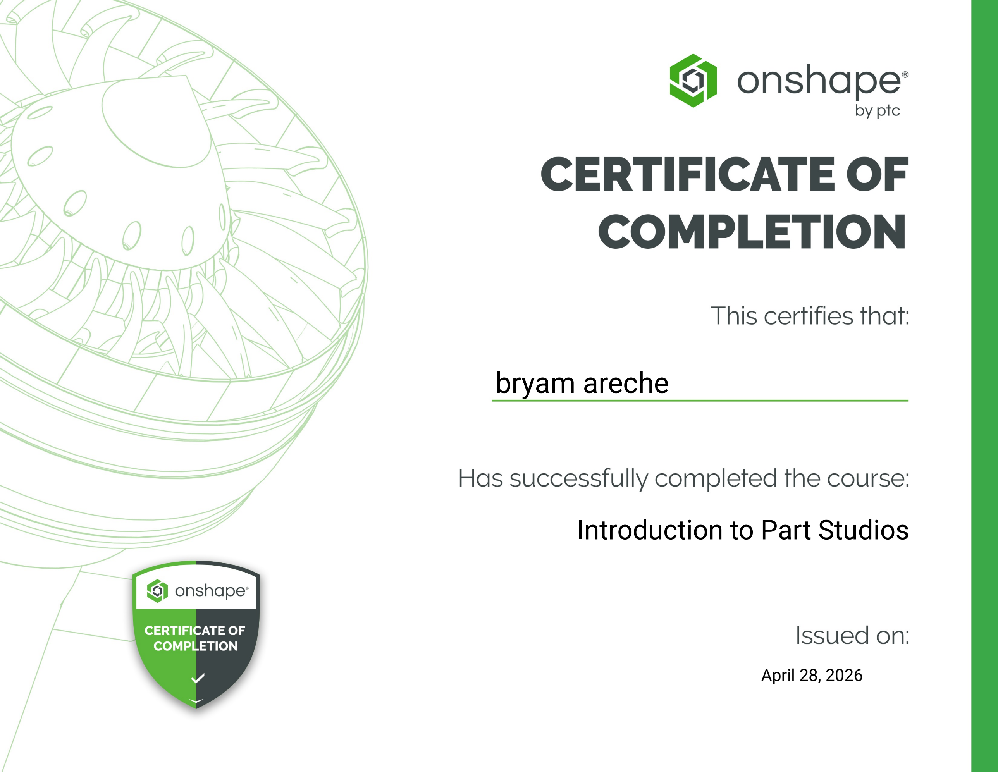
[picture p92: page 1]

bryam areche

Introduction to Part Studios

April 28, 2026
