DEADROSE6/FdD_Equipo_8/FundDiseño/Talleres/Taller mecánico de ONSHAPE/Certificado de angello/Introduction to Sketching.pdf

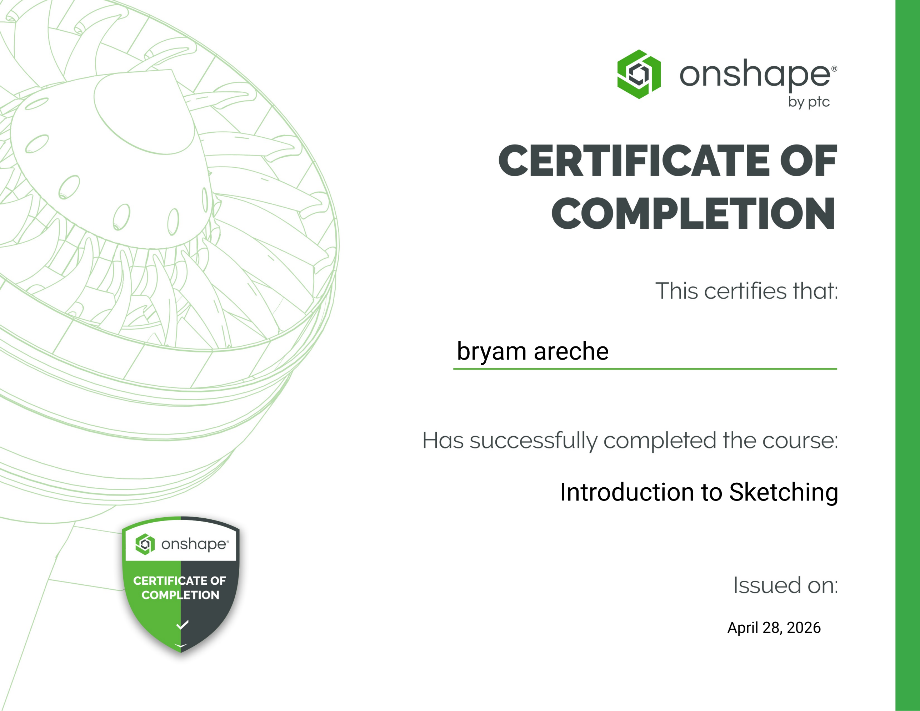
[picture p93: page 1]

bryam areche

Introduction to Sketching

April 28, 2026
