DEADROSE6/FdD_Equipo_8/Proyecto/MóduloMecánico/V2.0/Bocetos/Boceto V2.pdf

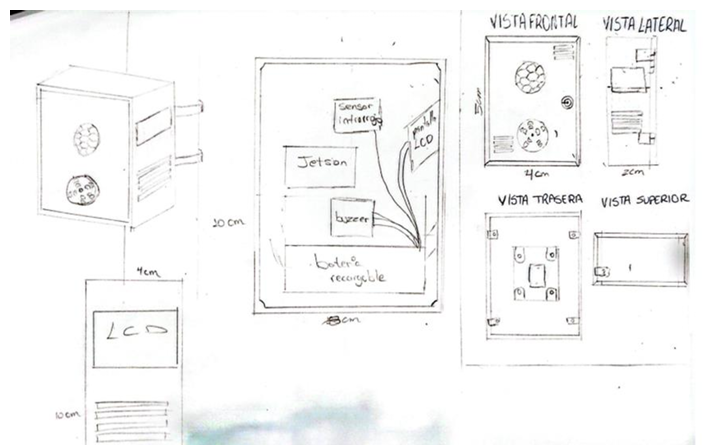
[picture p94: page 1]
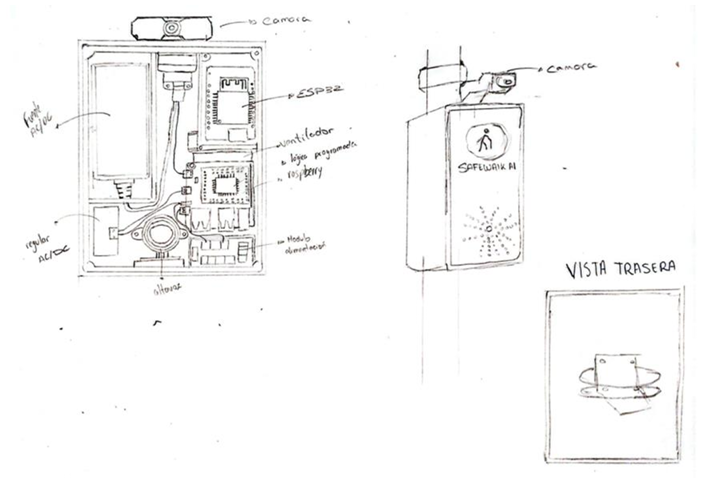
[picture p95: page 2]
