DEADROSE6/FdD_Equipo_8/Proyecto/MóduloMecánico/V1.0/Bocetos/Boceto V1.1.pdf

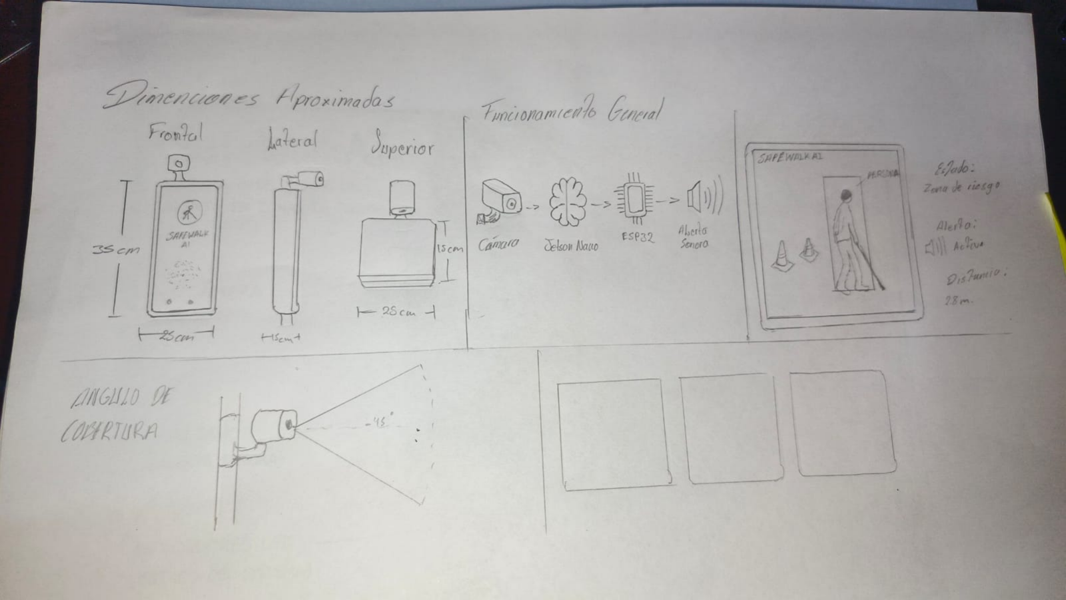
[picture p96: page 1]
