DEADROSE6/FdD_Equipo_8/Proyecto/MóduloMecánico/V1.0/Bocetos/Boceto V1.pdf

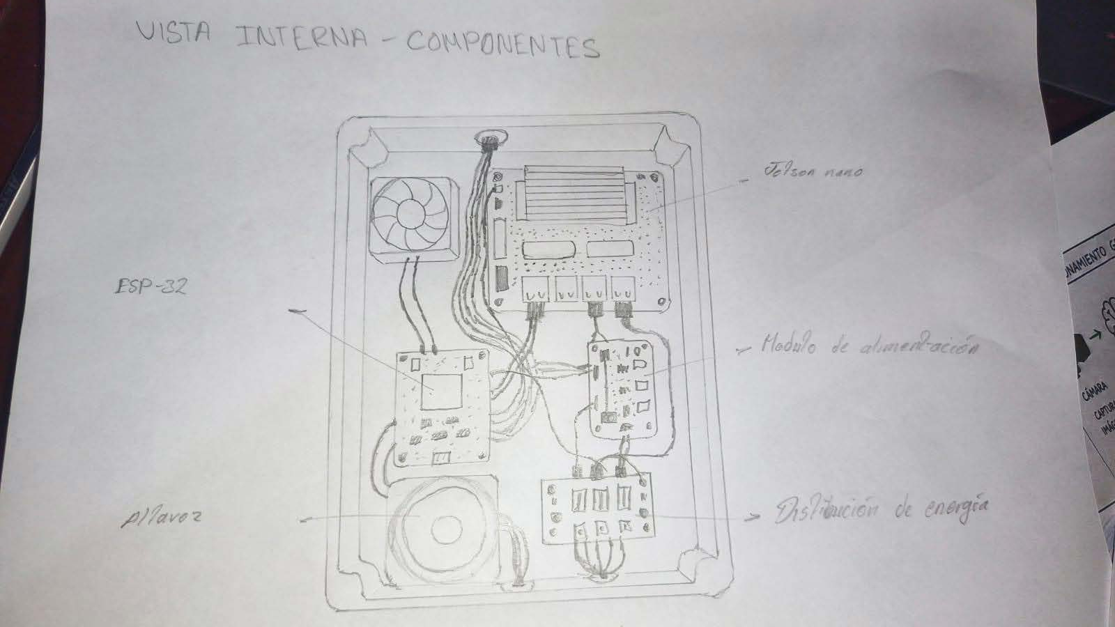
[picture p97: page 1]
