DEADROSE6/FdD_Equipo_8/FundDiseño/Talleres/Taller_10/Onshape Tomanguilla S/WhatsApp Image 2026-05-19 at 15.17.11.jpeg

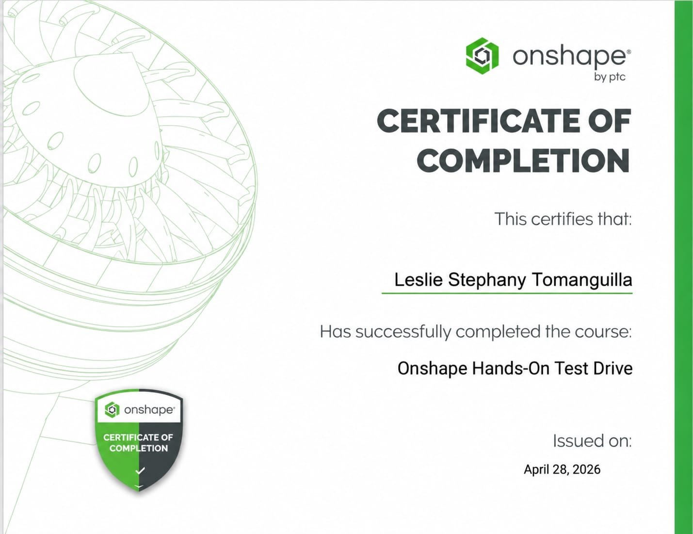
FundDiseño/Talleres/Taller_10/Onshape Tomanguilla S/WhatsApp Image 2026-05-19 at 15.17.11.jpeg
