DEADROSE6/FdD_Equipo_8/Recursos/Imagenes/img1.jpeg

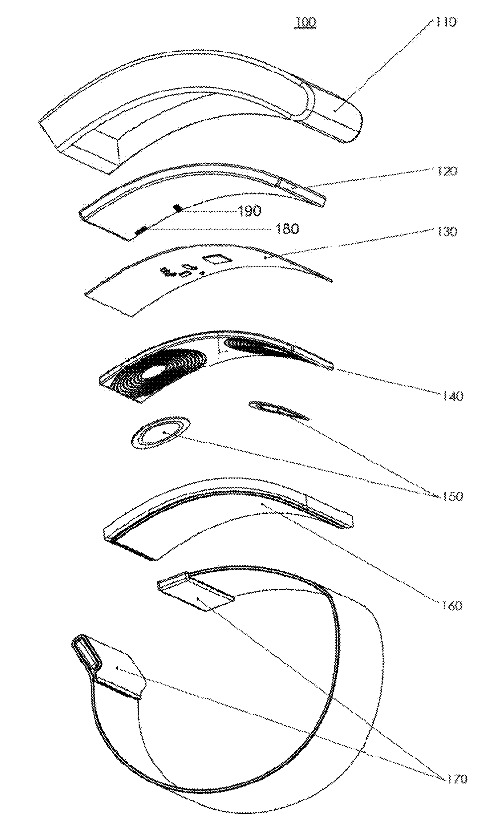
Recursos/Imagenes/img1.jpeg
