DEADROSE6/FdD_Equipo_8/Recursos/Imagenes/img2.jpeg

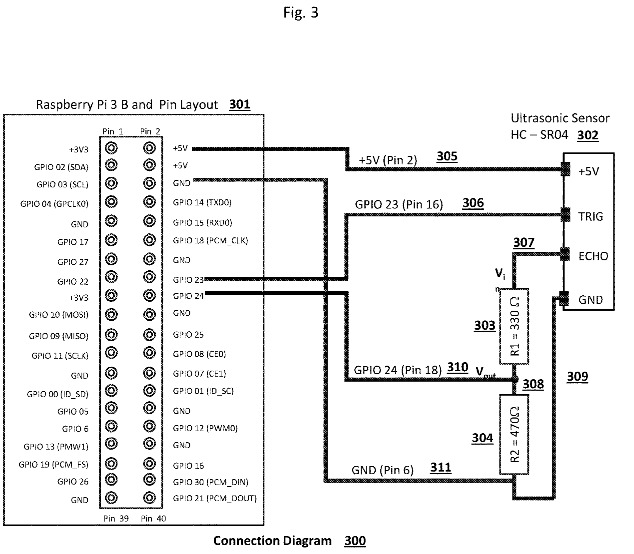
Recursos/Imagenes/img2.jpeg
