DEADROSE6/FdD_Equipo_8/Recursos/Imagenes/img3.jpeg

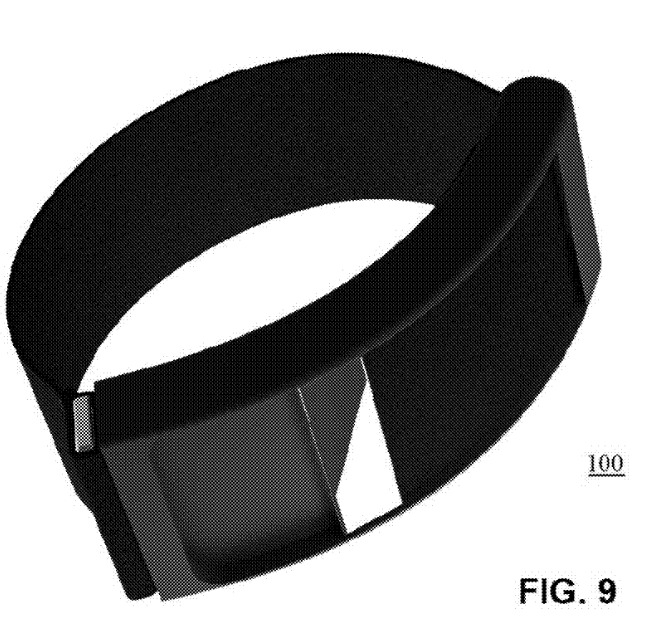
Recursos/Imagenes/img3.jpeg
