DEADROSE6/FdD_Equipo_8/Recursos/Imagenes/img4.jpeg

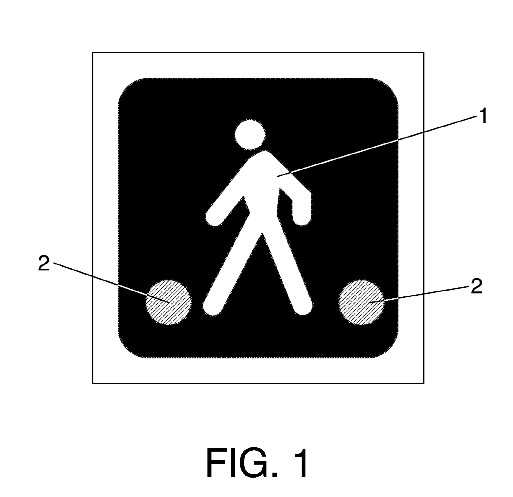
Recursos/Imagenes/img4.jpeg
