DEADROSE6/FdD_Equipo_8/Recursos/Imagenes/img5.jpeg

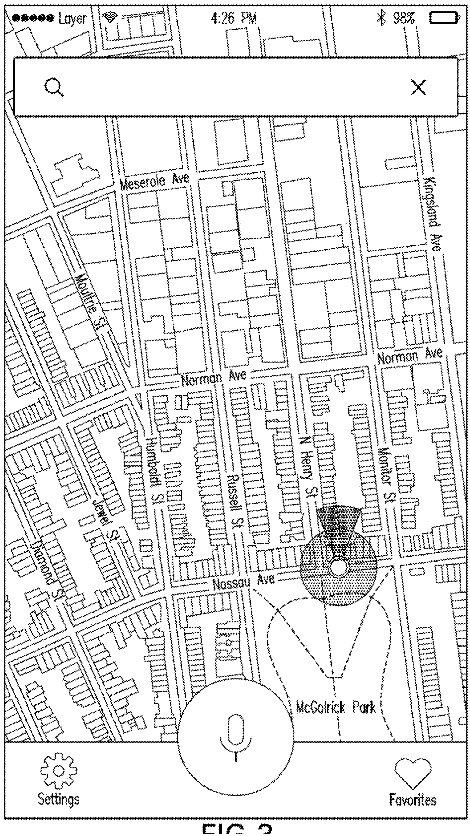
Recursos/Imagenes/img5.jpeg
