DEADROSE6/FdD_Equipo_8/Recursos/Imagenes/img6.jpeg

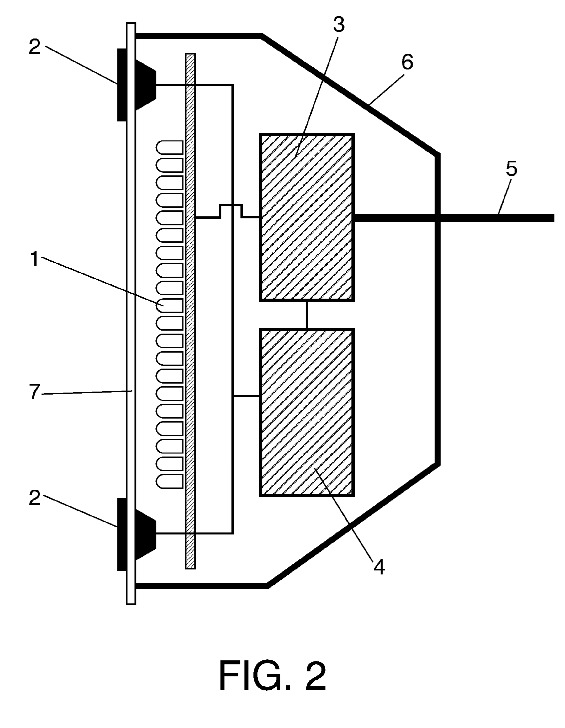
Recursos/Imagenes/img6.jpeg
