DEADROSE6/FdD_Equipo_8/Recursos/Imagenes/img7.jpeg

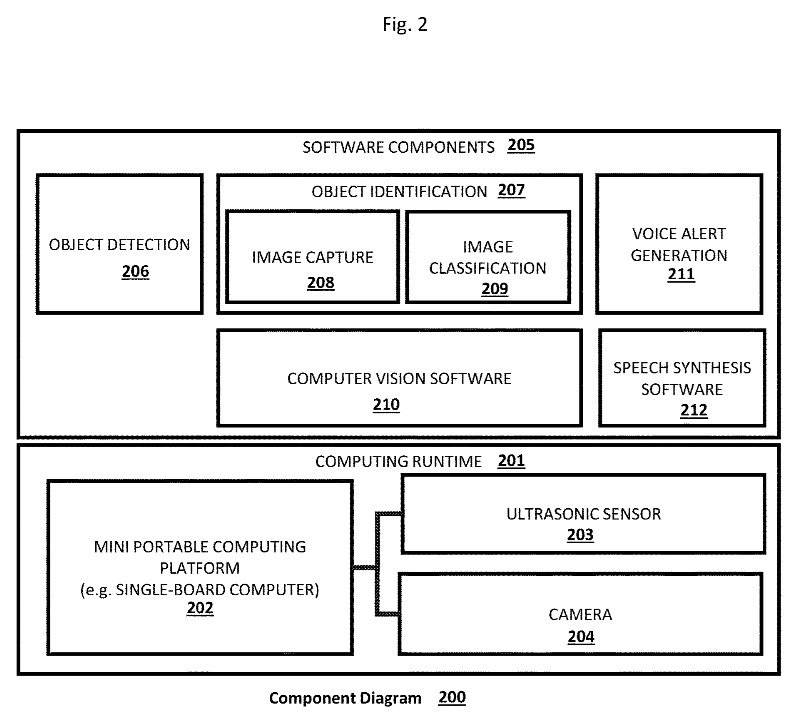
Recursos/Imagenes/img7.jpeg
