DEADROSE6/FdD_Equipo_8/Recursos/Imagenes/img8.jpeg

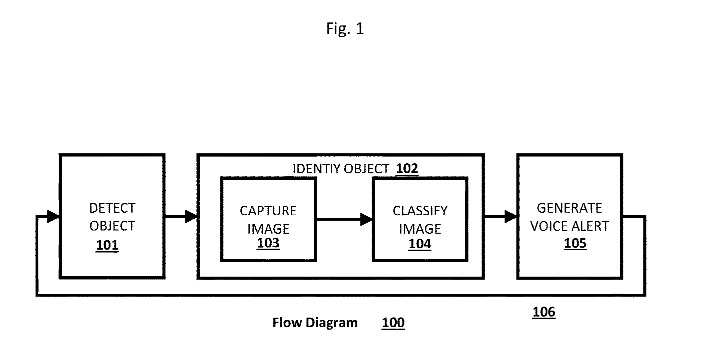
Recursos/Imagenes/img8.jpeg
