DEADROSE6/FdD_Equipo_8/Recursos/Imagenes/img9.png

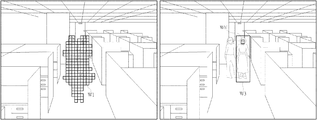
Recursos/Imagenes/img9.png
