DEADROSE6/FdD_Equipo_8/Recursos/Imagenes/img10.png

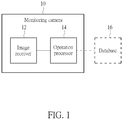
Recursos/Imagenes/img10.png
