DEADROSE6/FdD_Equipo_8/Proyecto/MóduloMecánico/Certificados/Alex Ccoyllo/Introduction to Onshape Assemblies.pdf

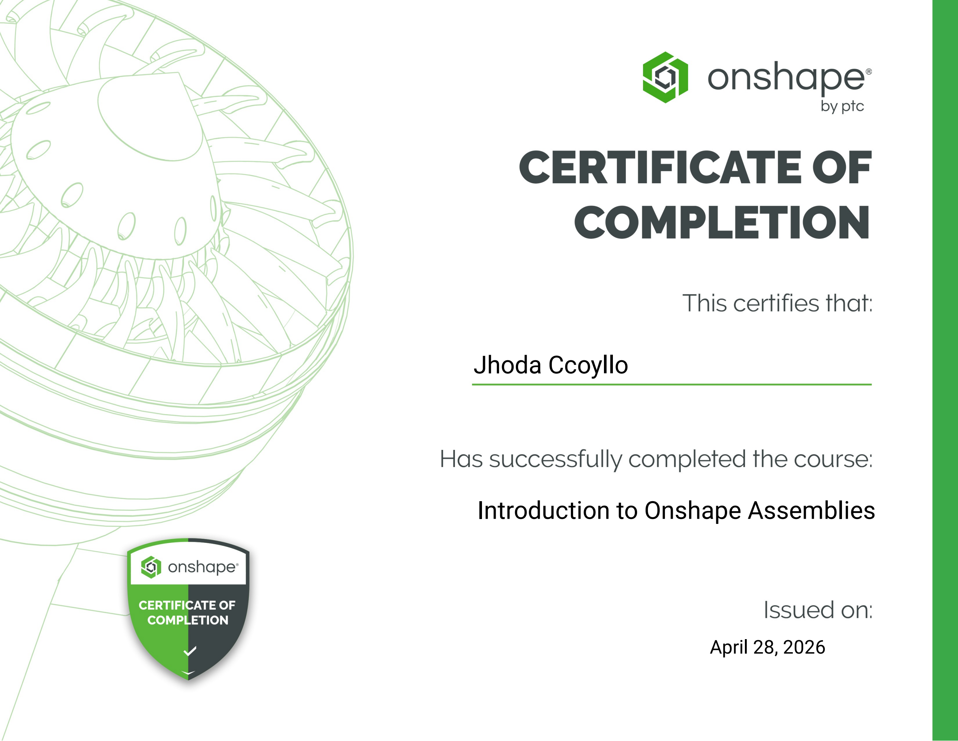
[picture p114: page 1]

Jhoda Ccoyllo

April 28, 2026

Introduction to Onshape Assemblies
