DEADROSE6/FdD_Equipo_8/Proyecto/MóduloMecánico/Certificados/Rolando Ronceros/Introduction to Onshape Assemblies (1).pdf

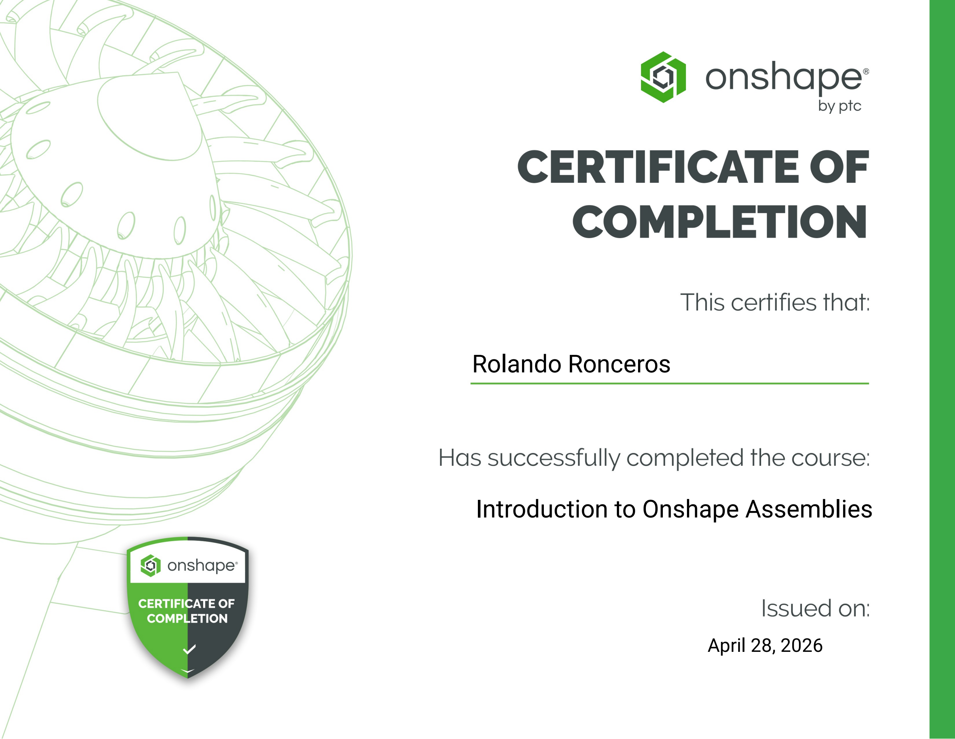
[picture p115: page 1]

Rolando Ronceros

April 28, 2026

Introduction to Onshape Assemblies
