DEADROSE6/FdD_Equipo_8/Proyecto/MóduloMecánico/Certificados/Alex Ccoyllo/Advanced Onshape Assemblies.pdf

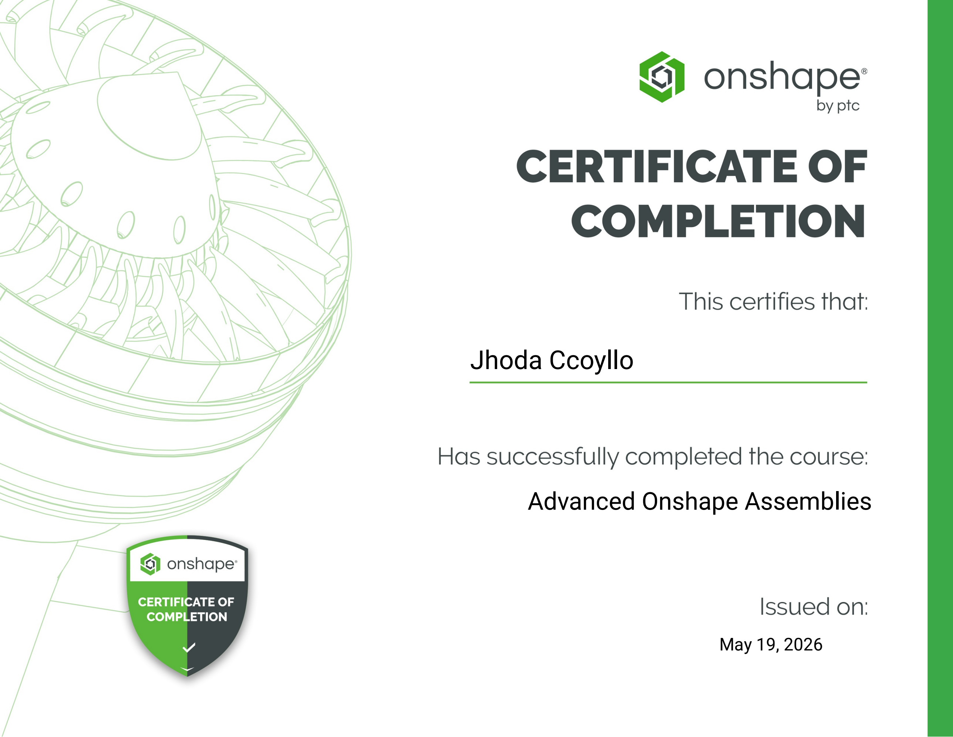
[picture p116: page 1]

Jhoda Ccoyllo

Advanced Onshape Assemblies

May 19, 2026
