DEADROSE6/FdD_Equipo_8/Proyecto/MóduloMecánico/Certificados/Daniela Mori/Advanced Onshape Assemblies-Mori.pdf

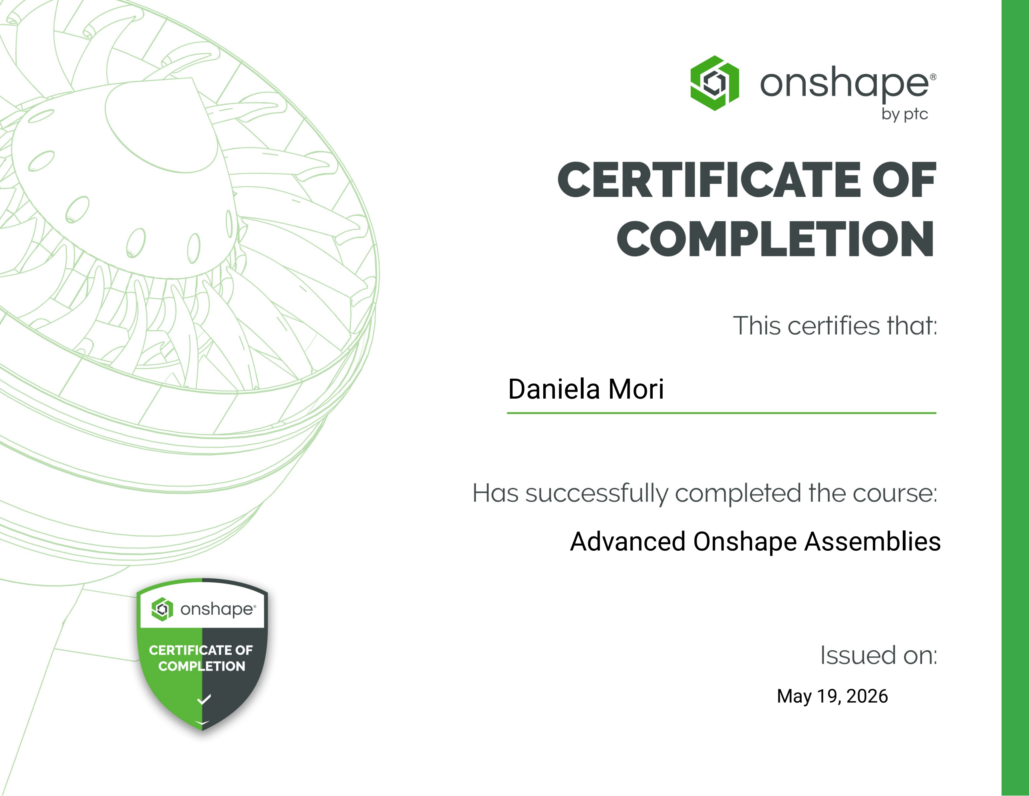
[picture p117: page 1]

Daniela Mori

Advanced Onshape Assemblies

May 19, 2026
