DEADROSE6/FdD_Equipo_8/FundDiseño/Talleres/Taller mecánico de ONSHAPE/Certificado de angello/Introduction to Onshape Assemblies.pdf

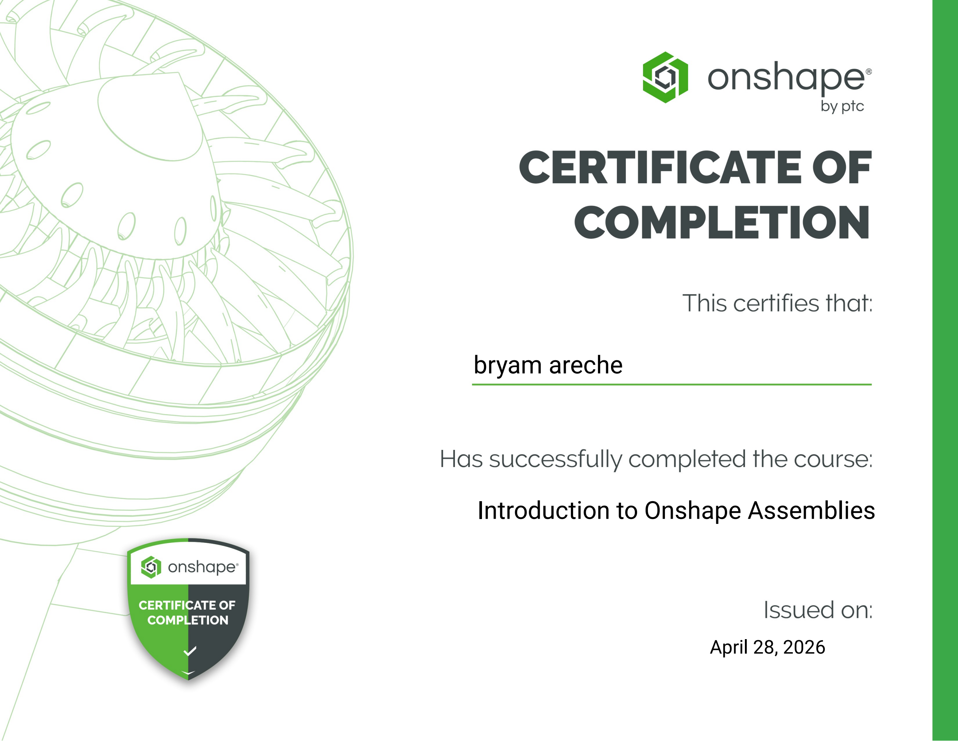
[picture p118: page 1]

bryam areche

April 28, 2026

Introduction to Onshape Assemblies
