DEADROSE6/FdD_Equipo_8/Proyecto/MóduloElectrónico/Esquema_electrónico_E08.pdf

# Módulo sensor de distancia Modulo Principal

# Módulo sensor de presencia

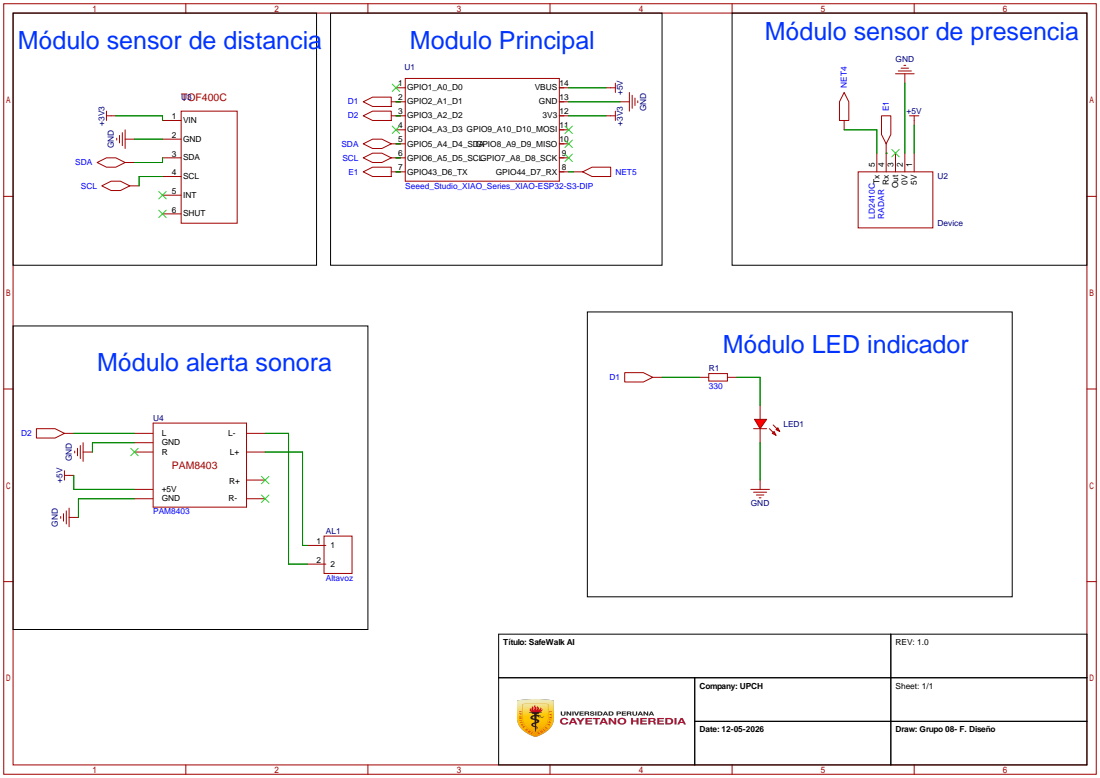
[picture p122: page 1]

Título: SafeWalk AI | REV: 1.0

Company: UPCH | Sheet: 1/1

Date: 12-05-2026 | Draw: Grupo 08- F. Diseño
