DEADROSE6/FdD_Equipo_8/Proyecto/MóduloMecánico/V3.0/Onshape/SoporteXIAO.pdf

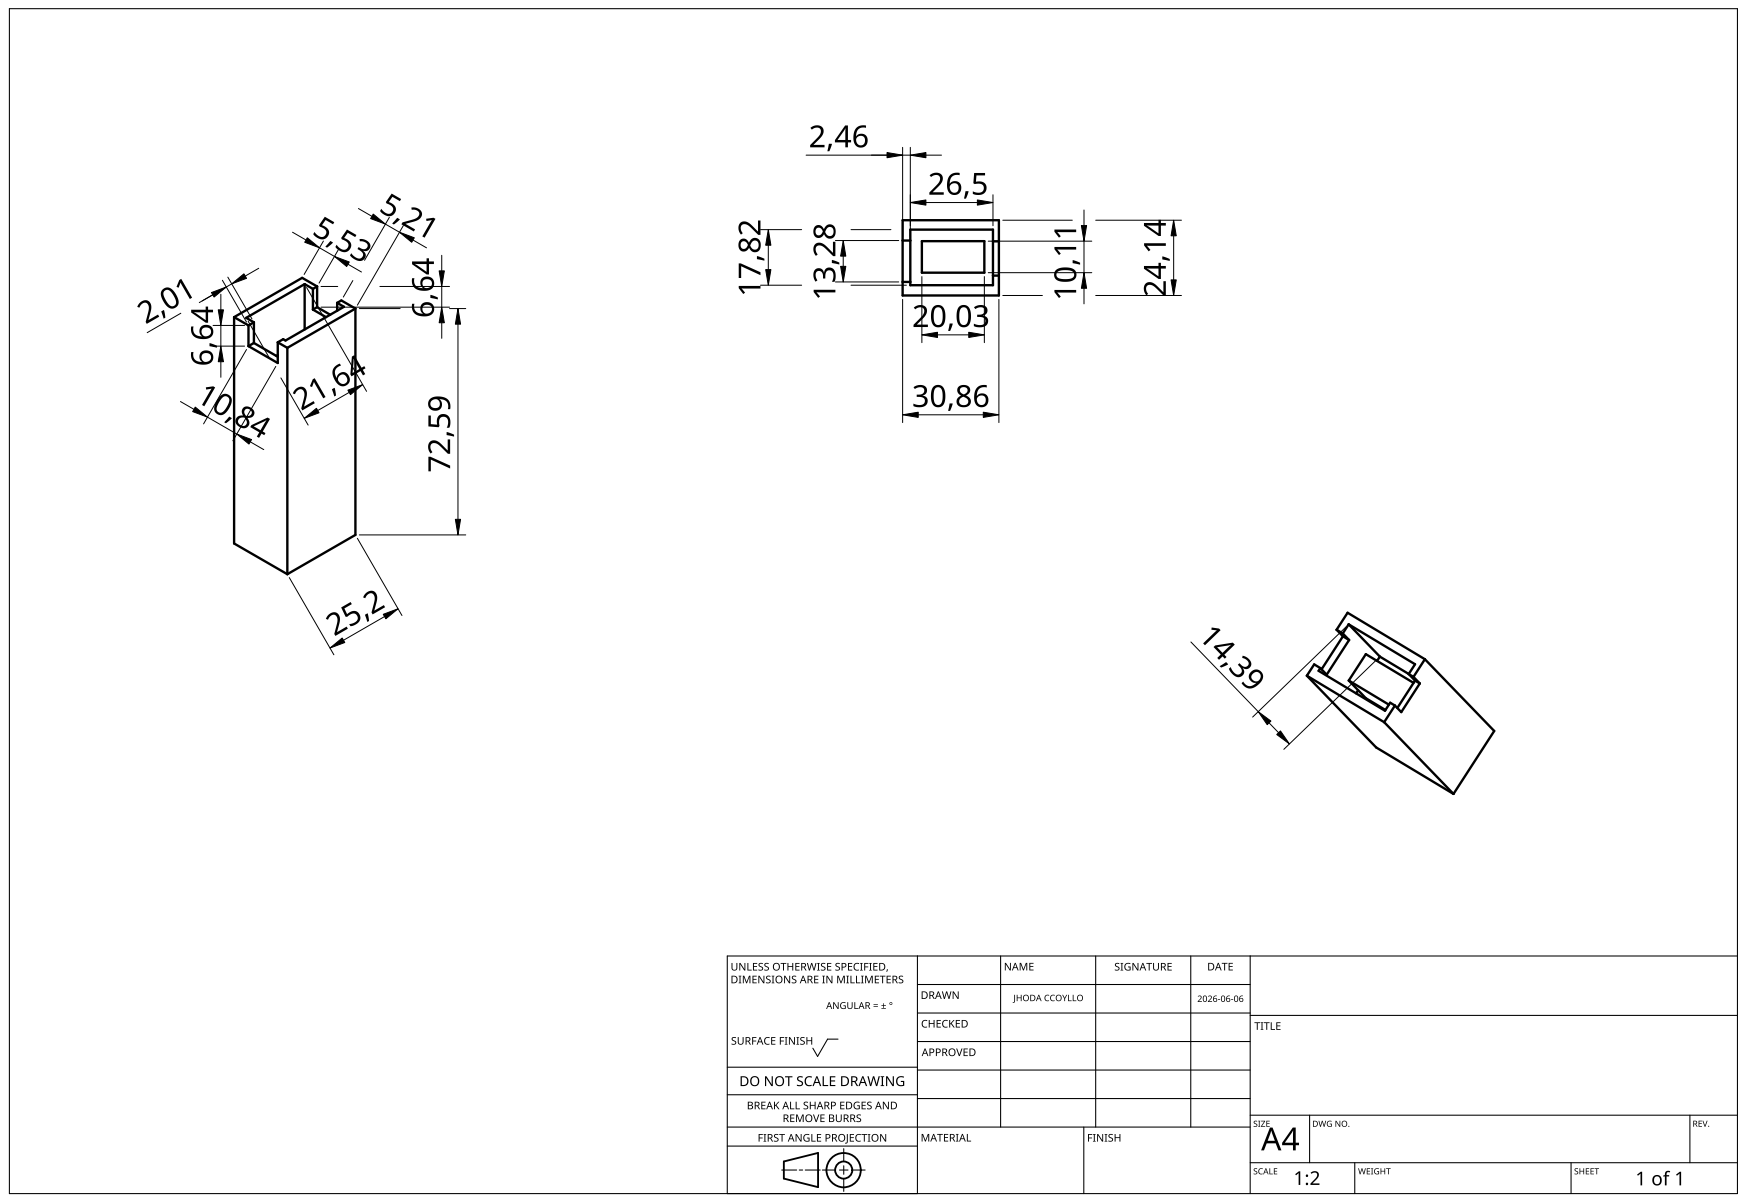
[picture p137: page 1]
