DEADROSE6/FdD_Equipo_8/Proyecto/MóduloMecánico/V3.0/Onshape/caja.pdf

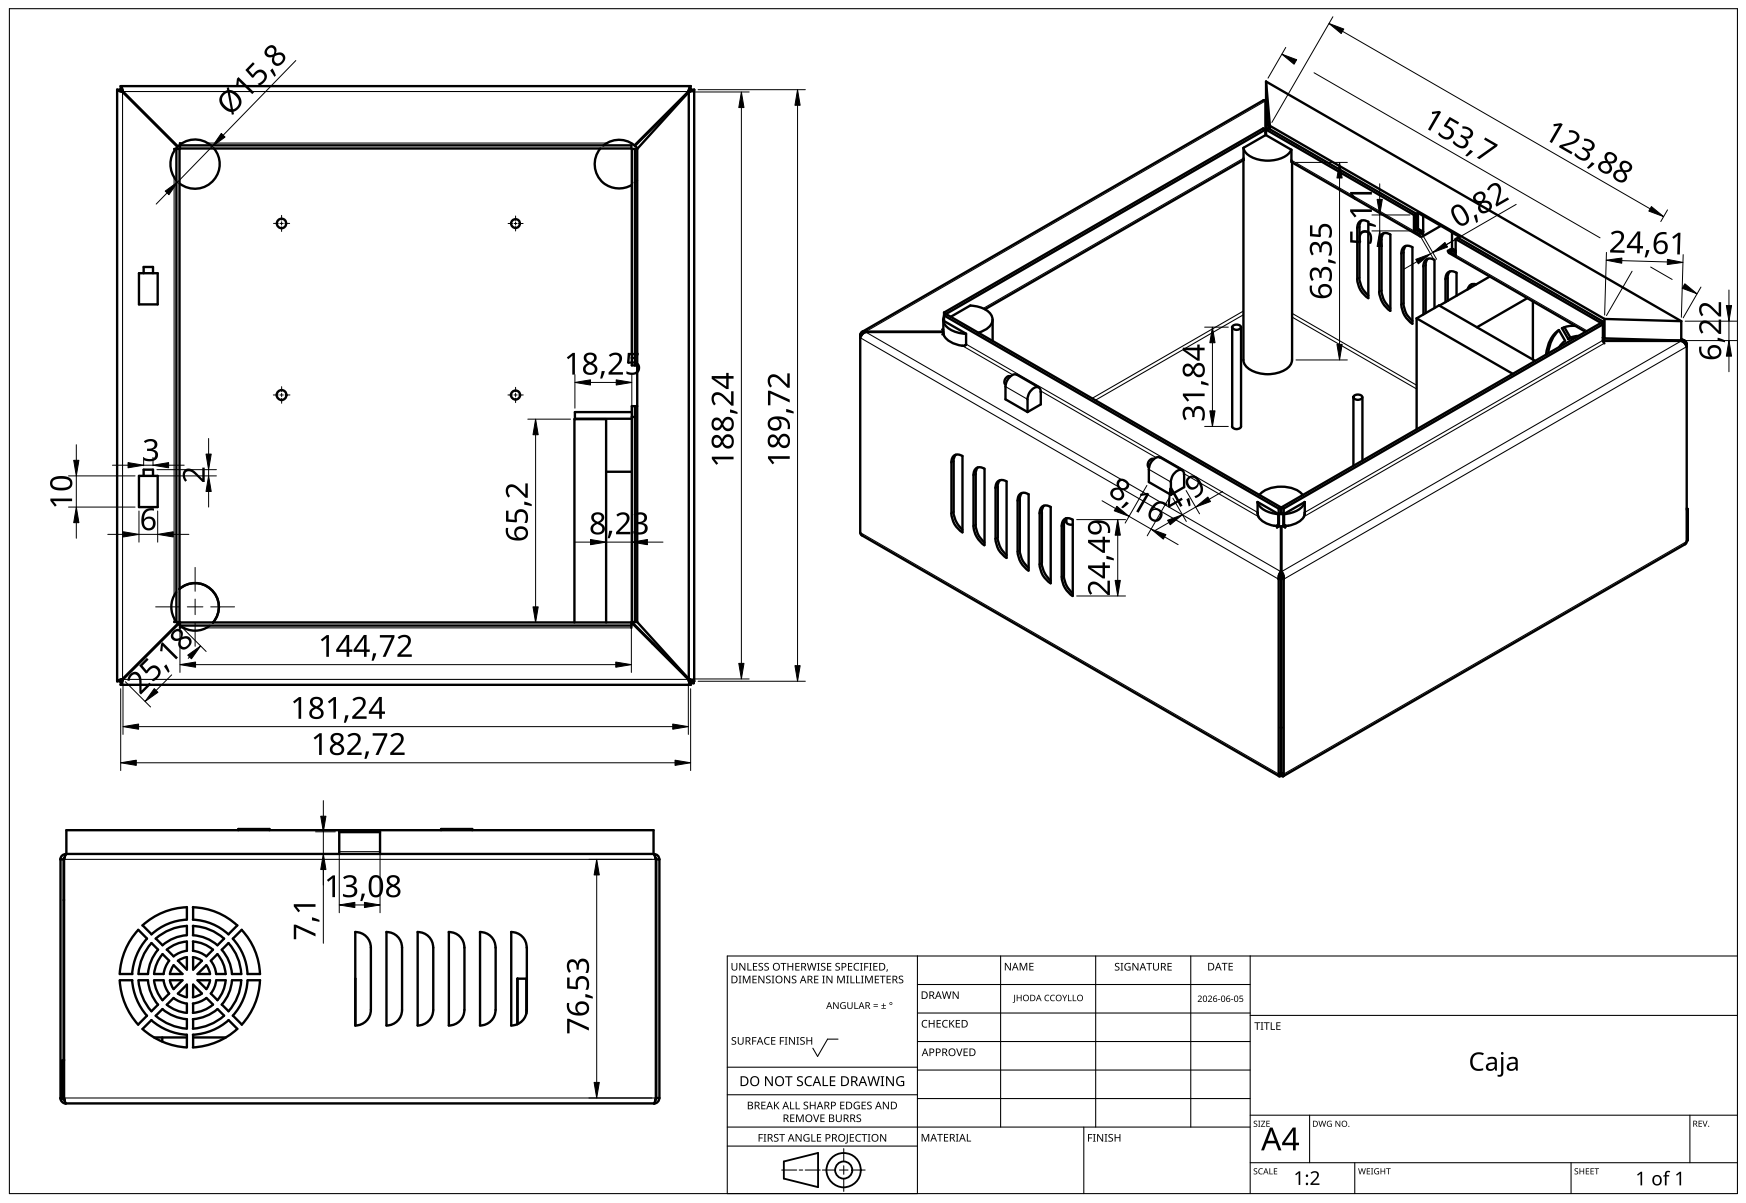
[picture p138: page 1]
