DEADROSE6/FdD_Equipo_8/Proyecto/MóduloMecánico/V2.0/Onshape/Tapa.pdf

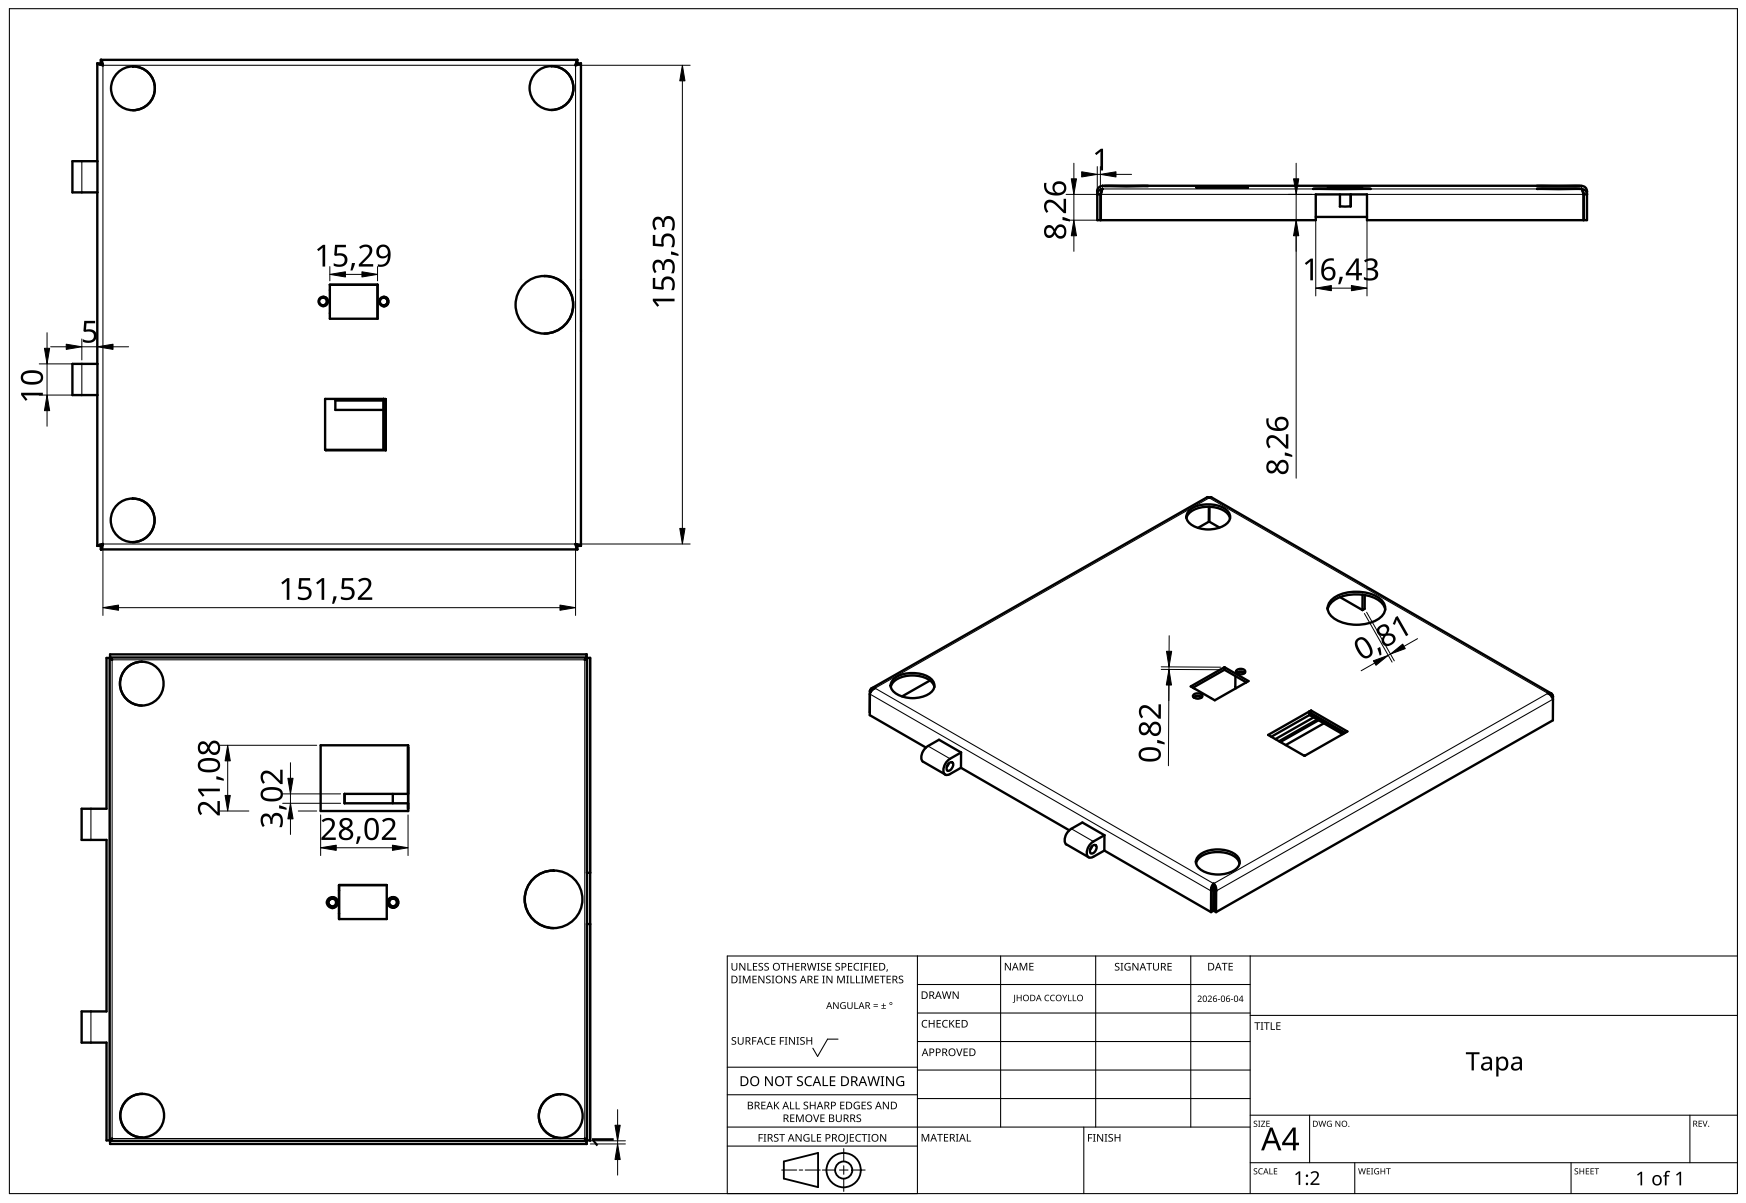
[picture p139: page 1]
